mihirsavadi/fancyGradHat/pcb_resources/fancyGradCap_rev2/fancyGradCap_rev2_ControlsPower.kicad_sch

## KiCad design pcb_resources/fancyGradCap_rev2/fancyGradCap_rev2_ControlsPower.kicad_sch (2022-02-05)

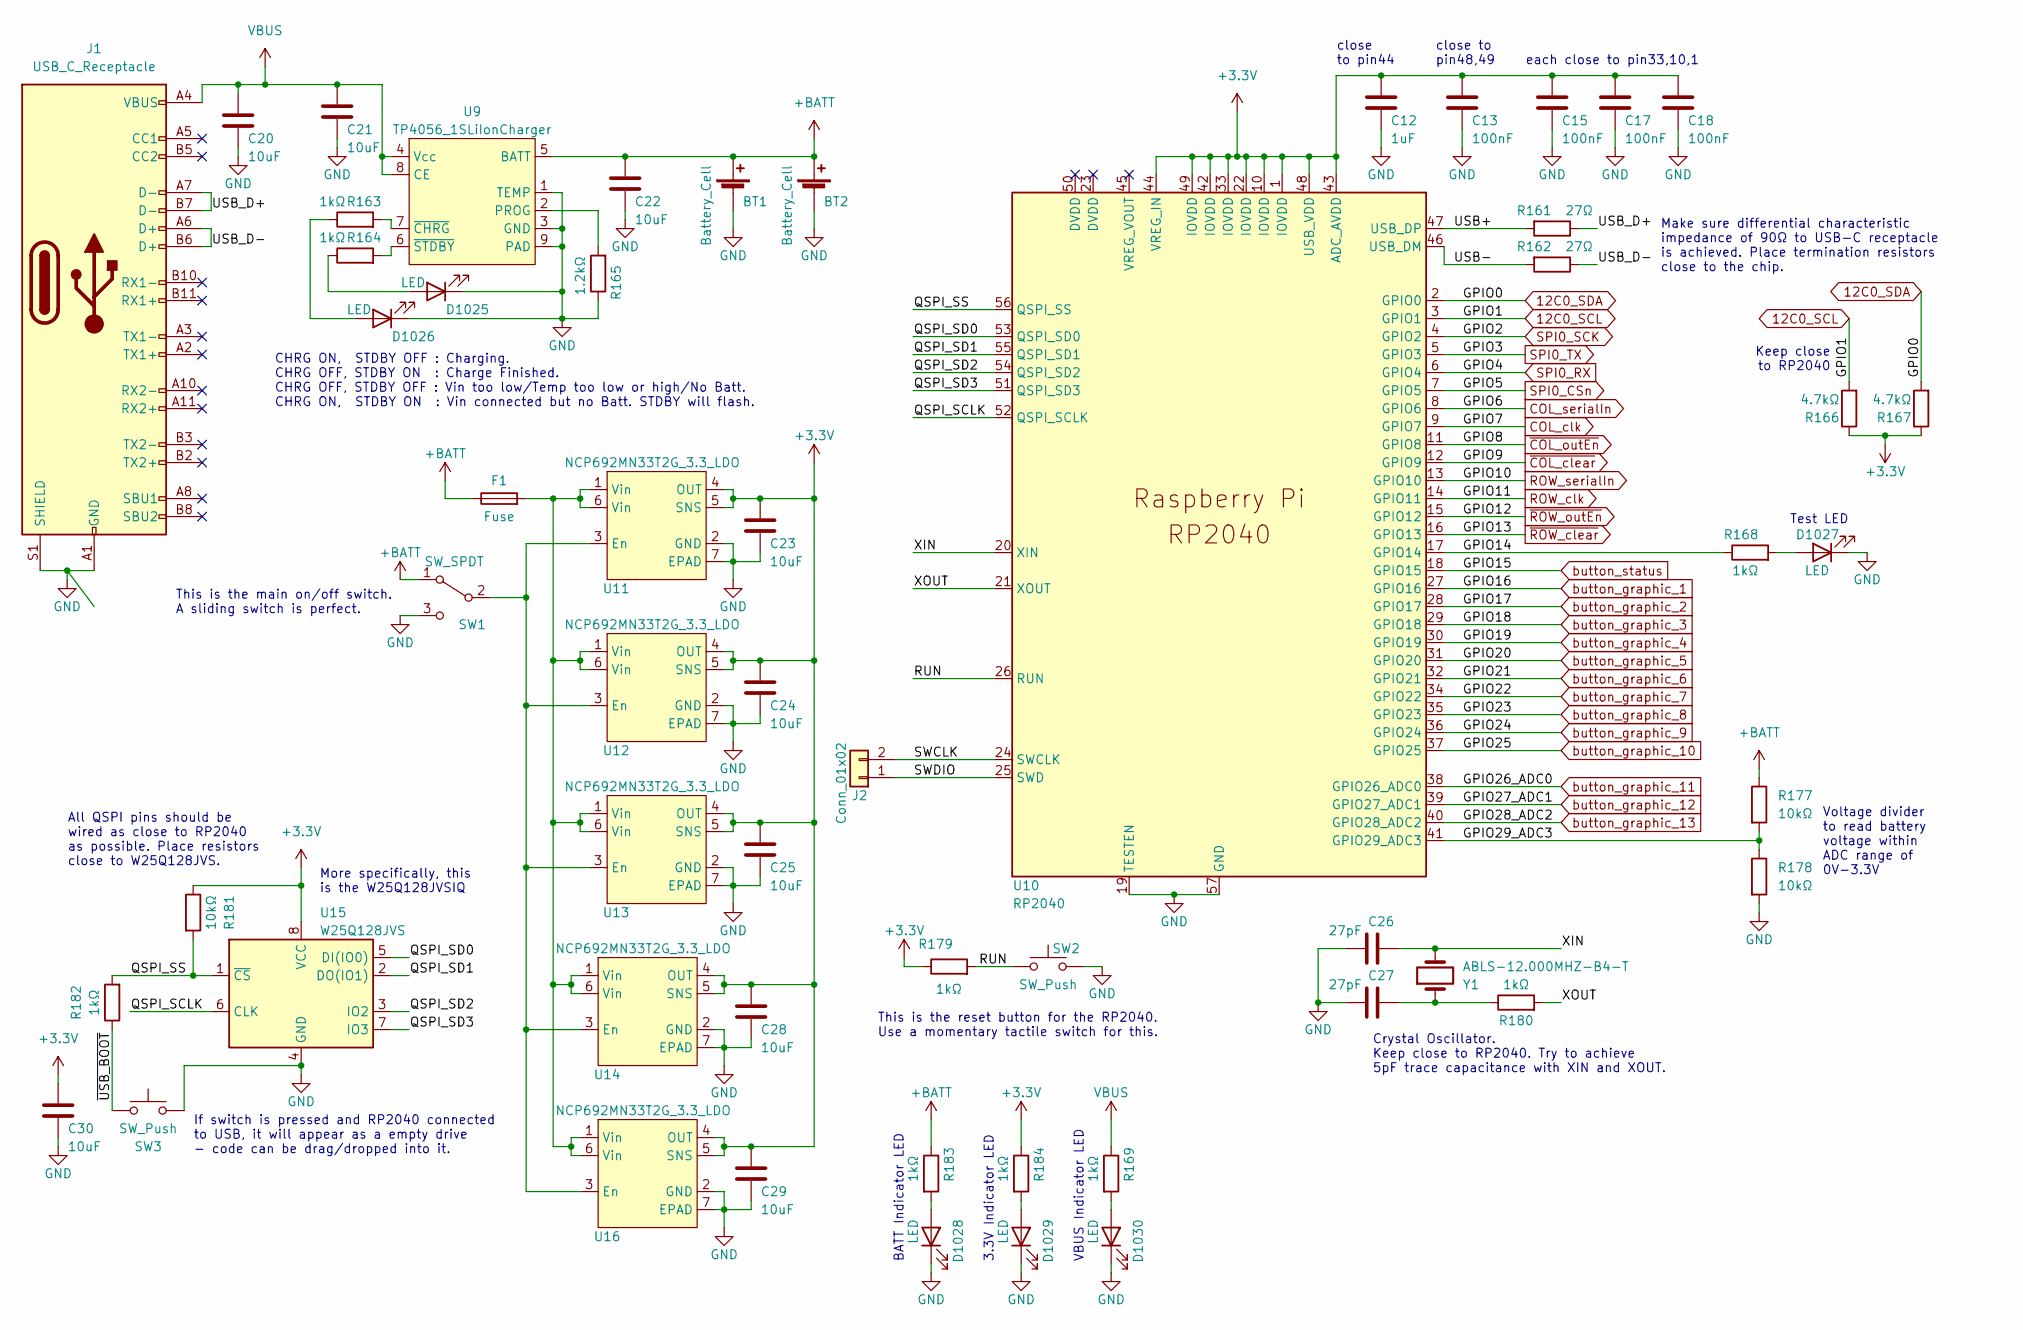
[picture p14: schematic fancyGradCap_rev2_ControlsPower.kicad_sch]

Parts:
BT1, BT2: Battery_Cell; BatteryHolder_Keystone_1042_1x18650
C12: 1uF; C_0603_1608Metric_Pad1.08x0.95mm_HandSolder
C13, C15, C17, C18: 100nF; C_0603_1608Metric_Pad1.08x0.95mm_HandSolder
C20, C21, C22, C23, C24, C25, C28, C29, C30: 10uF; C_0603_1608Metric_Pad1.08x0.95mm_HandSolder
C26, C27: 27pF; C_0603_1608Metric_Pad1.08x0.95mm_HandSolder
D1025, D1026, D1027, D1028, D1029, D1030: LED; LED_0603_1608Metric_Pad1.05x0.95mm_HandSolder
F1: Fuse; FuseHolder_Keystone_3550-2
J1: USB_C_Receptacle; USB_C_3.1_10137062-00021LF
J2: Conn_01x02; PinHeader_1x02_P2.54mm_Vertical
R161, R162: 27Ω; R_0603_1608Metric_Pad0.98x0.95mm_HandSolder
R163, R164, R168, R169, R179, R180, R182, R183, R184: 1kΩ; R_0603_1608Metric_Pad0.98x0.95mm_HandSolder
R165: 1.2kΩ; R_0603_1608Metric_Pad0.98x0.95mm_HandSolder
R166, R167: 4.7kΩ; R_0603_1608Metric_Pad0.98x0.95mm_HandSolder
R177, R178, R181: 10kΩ; R_0603_1608Metric_Pad0.98x0.95mm_HandSolder
SW1: SW_SPDT; SW_SPDT_CK-JS102011SAQN
SW2, SW3: SW_Push; SW_PUSH_1P1T_NO_6x6mm_H5mm
U9: TP4056_1SLiIonCharger
U10: RP2040; MCU_RP2040_QFN40P700X700X90-57N
U11, U12, U13, U14, U16: NCP692MN33T2G_3.3_LDO; DFN-6-1EP_3x3mm_P0.95mm_EP1.7x2.6mm
U15: W25Q128JVS; SOIC-8_5.23x5.23mm_P1.27mm
Y1: ABLS-12.000MHZ-B4-T; Crystal_ABLS-12.000MHZ-B4-T

Connections:
12C0_SCL: R166.2, U10.3 (GPIO1)
12C0_SDA: R167.2, U10.2 (GPIO0)
+3.3V: C12.1, C13.1, C15.1, C17.1, C18.1, C23.1, C24.1, C25.1, C28.1, C29.1, C30.1, R166.1, R167.1, R179.1, R181.1, R184.1, U10.1 (IOVDD), U10.10 (IOVDD), U10.22 (IOVDD), U10.33 (IOVDD), U10.42 (IOVDD), U10.43 (ADC_AVDD), U10.44 (VREG_IN), U10.48 (USB_VDD), U10.49 (IOVDD), U11.4 (OUT), U11.5 (SNS), U12.4 (OUT), U12.5 (SNS), U13.4 (OUT), U13.5 (SNS), U14.4 (OUT), U14.5 (SNS), U15.8 (VCC), U16.4 (OUT), U16.5 (SNS)
+BATT: BT1.1 (+), BT2.1 (+), C22.1, F1.1, R177.1, R183.1, SW1.1 (A), U9.5 (BATT)
COL_clk: U10.9 (GPIO7)
COL_serialIn: U10.8 (GPIO6)
GND: BT1.2 (-), BT2.2 (-), C12.2, C13.2, C15.2, C17.2, C18.2, C20.2, C21.2, C22.2, C23.2, C24.2, C25.2, C26.1, C27.1, C28.2, C29.2, C30.2, D1025.1 (K), D1026.1 (K), D1027.1 (K), D1028.1 (K), D1029.1 (K), D1030.1 (K), J1.A1 (GND), J1.A12 (GND), J1.B1 (GND), J1.B12 (GND), J1.S1 (SHIELD), R165.1, R178.2, SW1.3 (C), SW2.2, SW3.2, U9.1 (TEMP), U9.3 (GND), U9.9 (PAD), U10.19 (TESTEN), U10.57 (GND), U11.2 (GND), U11.7 (EPAD), U12.2 (GND), U12.7 (EPAD), U13.2 (GND), U13.7 (EPAD), U14.2 (GND), U14.7 (EPAD), U15.4 (GND), U16.2 (GND), U16.7 (EPAD)
GPIO14: R168.1, U10.17 (GPIO14)
GPIO29_ADC3: R177.2, R178.1, U10.41 (GPIO29_ADC3)
unnamed: C27.2, R180.1, Y1.1
unnamed: D1025.2 (A), R164.1
unnamed: D1026.2 (A), R163.1
unnamed: D1027.2 (A), R168.2
unnamed: D1028.2 (A), R183.2
unnamed: D1029.2 (A), R184.2
unnamed: D1030.2 (A), R169.2
unnamed: F1.2, U11.1 (Vin), U11.6 (Vin), U12.1 (Vin), U12.6 (Vin), U13.1 (Vin), U13.6 (Vin), U14.1 (Vin), U14.6 (Vin), U16.1 (Vin), U16.6 (Vin)
unnamed: R163.2, U9.7 (~CHRG)
unnamed: R164.2, U9.6 (~STDBY)
unnamed: R165.2, U9.2 (PROG)
unnamed: SW1.2 (B), U11.3 (En), U12.3 (En), U13.3 (En), U14.3 (En), U16.3 (En)
QSPI_SCLK: U10.52 (QSPI_SCLK), U15.6 (CLK)
QSPI_SD0: U10.53 (QSPI_SD0), U15.5 (DI(IO0))
QSPI_SD1: U10.55 (QSPI_SD1), U15.2 (DO(IO1))
QSPI_SD2: U10.54 (QSPI_SD2), U15.3 (IO2)
QSPI_SD3: U10.51 (QSPI_SD3), U15.7 (IO3)
QSPI_SS: R181.2, R182.2, U10.56 (QSPI_SS), U15.1 (~CS)
ROW_clk: U10.14 (GPIO11)
ROW_serialIn: U10.13 (GPIO10)
RUN: R179.2, SW2.1, U10.26 (RUN)
SPI0_CSn: U10.7 (GPIO5)
SPI0_RX: U10.6 (GPIO4)
SPI0_SCK: U10.4 (GPIO2)
SPI0_TX: U10.5 (GPIO3)
SWCLK: J2.2, U10.24 (SWCLK)
SWDIO: J2.1, U10.25 (SWD)
USB+: R161.2, U10.47 (USB_DP)
USB-: R162.2, U10.46 (USB_DM)
USB_D+: J1.A7 (D-), J1.B7 (D-), R161.1
USB_D-: J1.A6 (D+), J1.B6 (D+), R162.1
VBUS: C20.1, C21.1, J1.A4 (VBUS), J1.A9 (VBUS), J1.B4 (VBUS), J1.B9 (VBUS), R169.1, U9.4 (Vcc), U9.8 (CE)
XIN: C26.2, U10.20 (XIN), Y1.2
XOUT: R180.2, U10.21 (XOUT)
button_graphic_1: U10.27 (GPIO16)
button_graphic_2: U10.28 (GPIO17)
button_graphic_3: U10.29 (GPIO18)
button_graphic_4: U10.30 (GPIO19)
button_graphic_5: U10.31 (GPIO20)
button_graphic_6: U10.32 (GPIO21)
button_graphic_7: U10.34 (GPIO22)
button_graphic_8: U10.35 (GPIO23)
button_graphic_9: U10.36 (GPIO24)
button_graphic_10: U10.37 (GPIO25)
button_graphic_11: U10.38 (GPIO26_ADC0)
button_graphic_12: U10.39 (GPIO27_ADC1)
button_graphic_13: U10.40 (GPIO28_ADC2)
button_status: U10.18 (GPIO15)
~COL_clear: U10.12 (GPIO9)
~COL_outEn: U10.11 (GPIO8)
~ROW_clear: U10.16 (GPIO13)
~ROW_outEn: U10.15 (GPIO12)
~USB_BOOT: R182.1, SW3.1

Notes on the sheet:
Voltage divider to read battery voltage within ADC range of 0V-3.3V
Test LED
BATT Indicator LED
Crystal Oscillator. Keep close to RP2040. Try to achieve 5pF trace capacitance with XIN and XOUT.
Keep close to RP2040
close to pin44
Make sure differential characteristic impedance of 90Ω to USB-C receptacle is achieved. Place termination resistors close to the chip.
All QSPI pins should be wired as close to RP2040 as possible. Place resistors close to W25Q128JVS.
This is the reset button for the RP2040. Use a momentary tactile switch for this.
More specifically, this is the W25Q128JVSIQ
If switch is pressed and RP2040 connected to USB, it will appear as a empty drive - code can be drag/dropped into it.
CHRG ON, STDBY OFF : Charging. CHRG OFF, STDBY ON : Charge Finished. CHRG OFF, STDBY OFF : Vin too low/Temp too low or high/No Batt. CHRG ON, STDBY ON : Vin connected but no Batt. STDBY will flash.
3.3V Indicator LED
each close to pin33,10,1
This is the main on/off switch. A sliding switch is perfect.
close to pin48,49
VBUS Indicator LED
