mihirsavadi/fancyGradHat/pcb_resources/fancyGradCap_rev2/fancyGradCap_rev2_LEDDriverCircuitry.kicad_sch

## KiCad design pcb_resources/fancyGradCap_rev2/fancyGradCap_rev2_LEDDriverCircuitry.kicad_sch (2022-02-05)

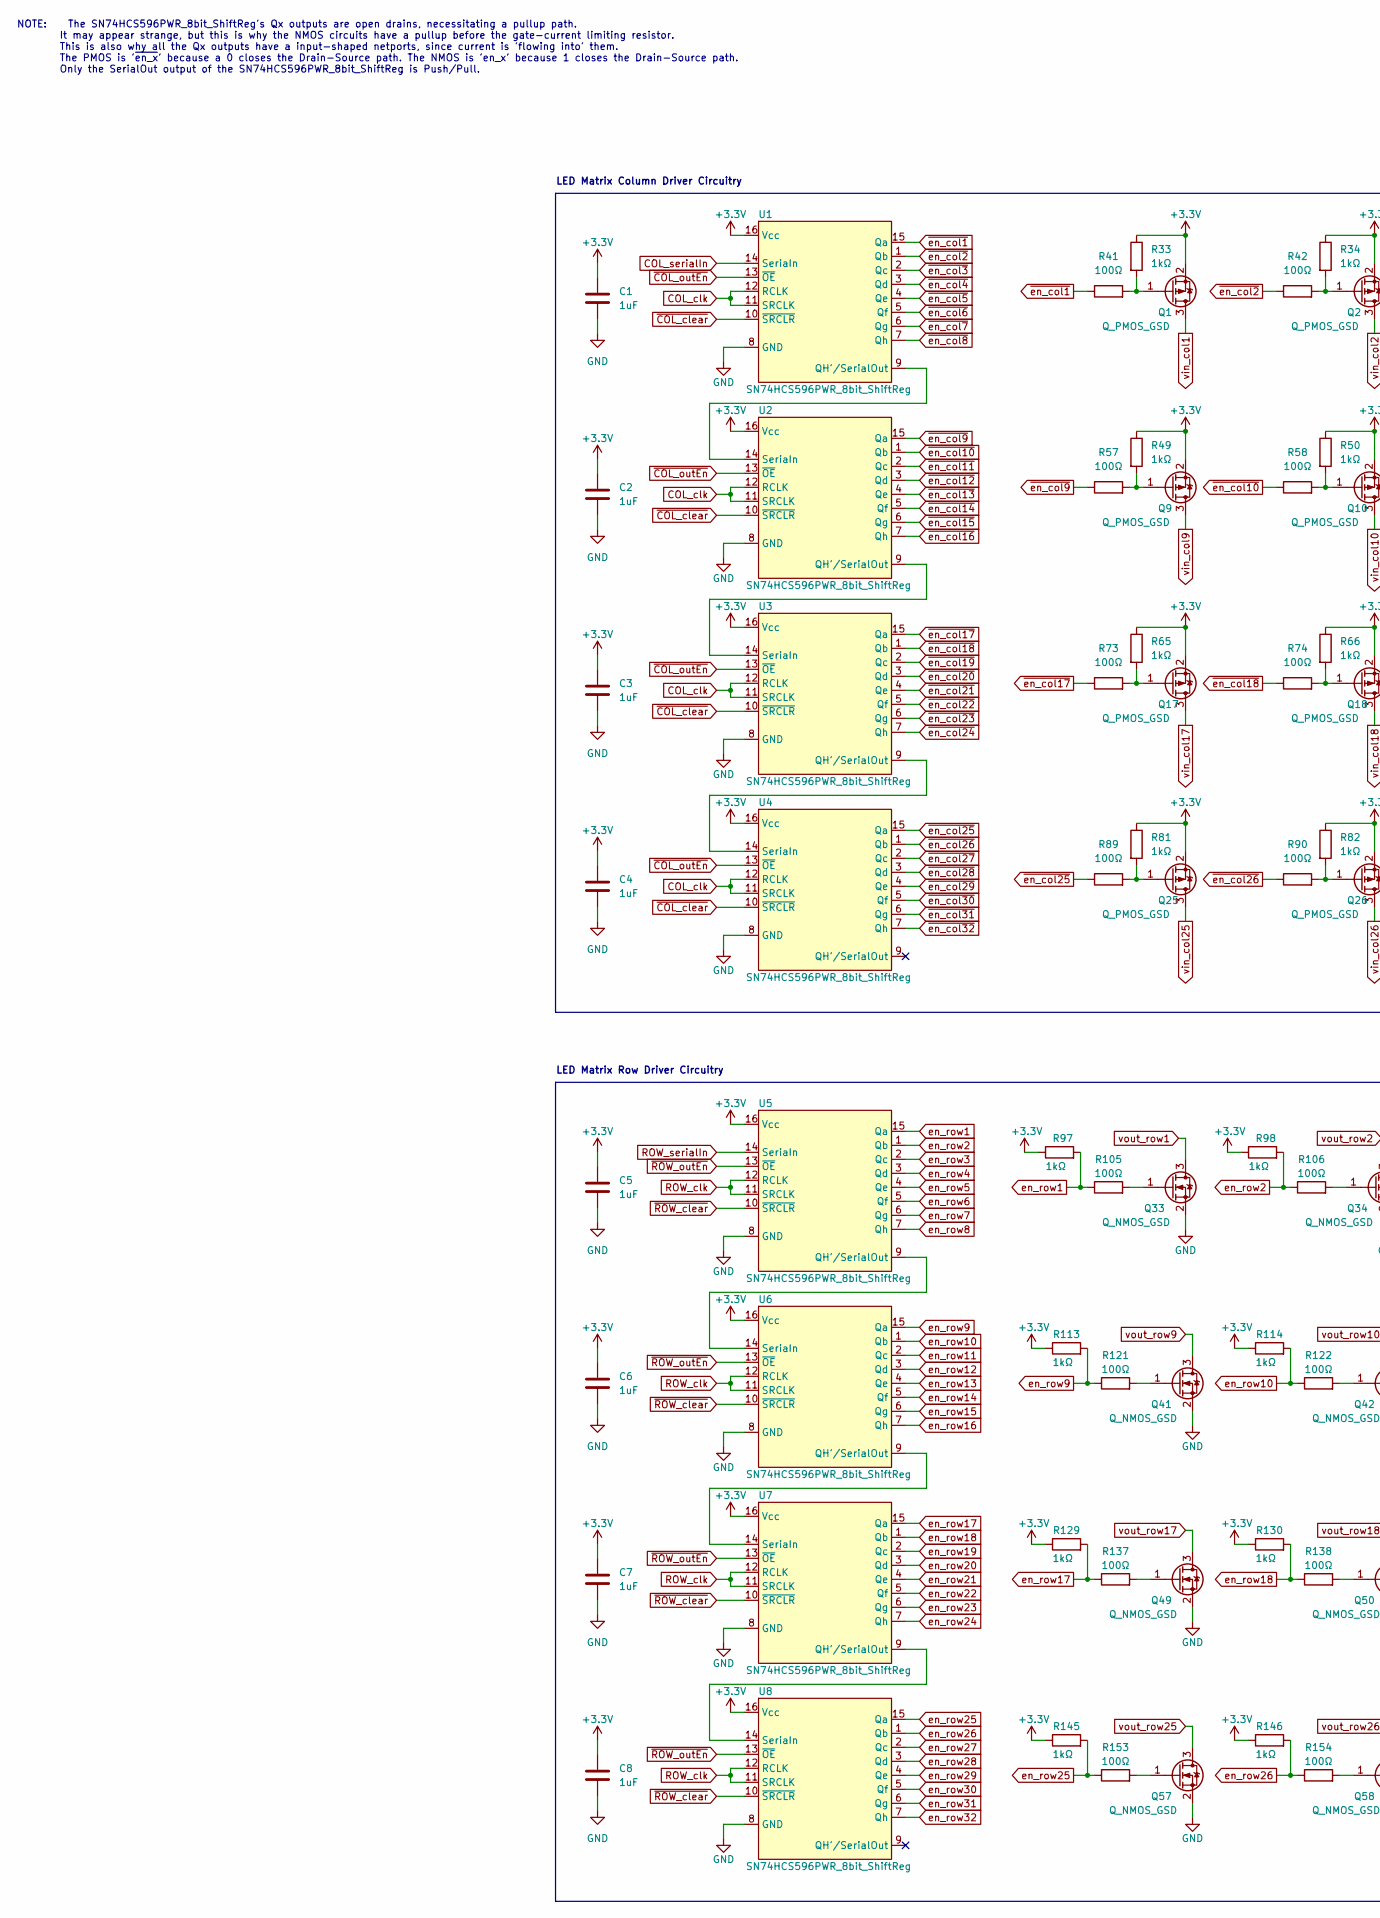
[picture p15: schematic fancyGradCap_rev2_LEDDriverCircuitry.kicad_sch, part in row 1, column 1]

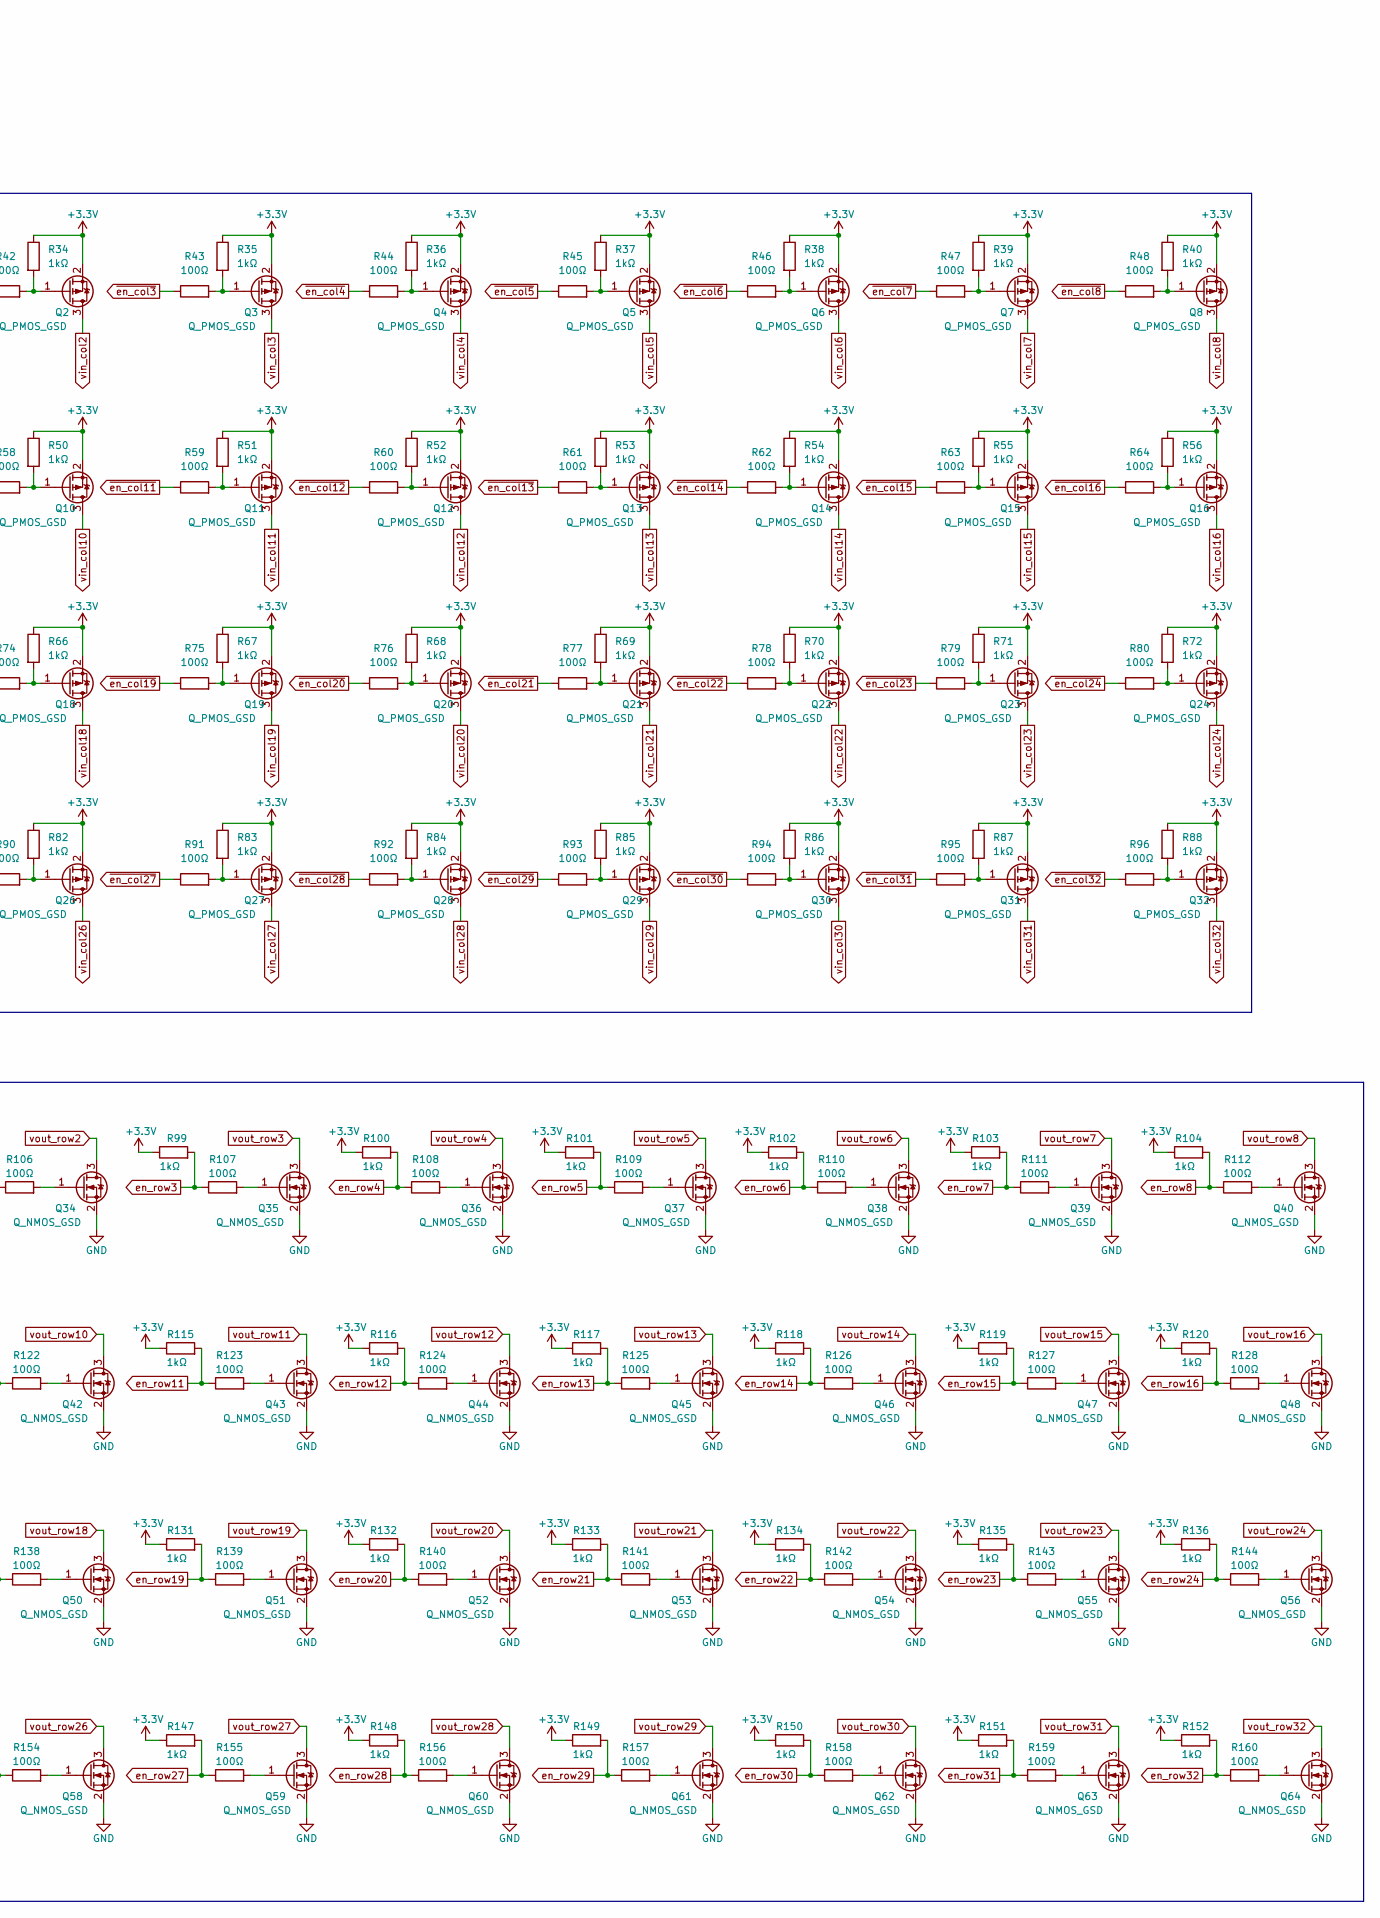
[picture p16: schematic fancyGradCap_rev2_LEDDriverCircuitry.kicad_sch, part in row 1, column 2]

Parts:
C1, C2, C3, C4, C5, C6, C7, C8: 1uF; C_0603_1608Metric_Pad1.08x0.95mm_HandSolder
Q1, Q2, Q3, Q4, Q5, Q6, Q7, Q8, Q9, Q10, Q11, Q12, Q13, Q14, Q15, Q16, Q17, Q18, Q19, Q20, Q21, Q22, Q23, Q24, Q25, Q26, Q27, Q28, Q29, Q30, Q31, Q32: Q_PMOS_GSD; SOT-23
Q33, Q34, Q35, Q36, Q37, Q38, Q39, Q40, Q41, Q42, Q43, Q44, Q45, Q46, Q47, Q48, Q49, Q50, Q51, Q52, Q53, Q54, Q55, Q56, Q57, Q58, Q59, Q60, Q61, Q62, Q63, Q64: Q_NMOS_GSD; SOT-23
R33, R34, R35, R36, R37, R38, R39, R40, R49, R50, R51, R52, R53, R54, R55, R56, R65, R66, R67, R68, R69, R70, R71, R72, R81, R82, R83, R84, R85, R86, R87, R88, R97, R98, R99, R100, R101, R102, R103, R104, R113, R114, R115, R116, R117, R118, R119, R120, R129, R130, R131, R132, R133, R134, R135, R136, R145, R146, R147, R148, R149, R150, R151, R152: 1kΩ; R_0603_1608Metric_Pad0.98x0.95mm_HandSolder
R41, R42, R43, R44, R45, R46, R47, R48, R57, R58, R59, R60, R61, R62, R63, R64, R73, R74, R75, R76, R77, R78, R79, R80, R89, R90, R91, R92, R93, R94, R95, R96, R105, R106, R107, R108, R109, R110, R111, R112, R121, R122, R123, R124, R125, R126, R127, R128, R137, R138, R139, R140, R141, R142, R143, R144, R153, R154, R155, R156, R157, R158, R159, R160: 100Ω; R_0603_1608Metric_Pad0.98x0.95mm_HandSolder
U1, U2, U3, U4, U5, U6, U7, U8: SN74HCS596PWR_8bit_ShiftReg; TSSOP-16_4.4x5mm_P0.65mm

Connections:
+3.3V: C1.1, C2.1, C3.1, C4.1, C5.1, C6.1, C7.1, C8.1, Q1.2 (S), Q2.2 (S), Q3.2 (S), Q4.2 (S), Q5.2 (S), Q6.2 (S), Q7.2 (S), Q8.2 (S), Q9.2 (S), Q10.2 (S), Q11.2 (S), Q12.2 (S), Q13.2 (S), Q14.2 (S), Q15.2 (S), Q16.2 (S), Q17.2 (S), Q18.2 (S), Q19.2 (S), Q20.2 (S), Q21.2 (S), Q22.2 (S), Q23.2 (S), Q24.2 (S), Q25.2 (S), Q26.2 (S), Q27.2 (S), Q28.2 (S), Q29.2 (S), Q30.2 (S), Q31.2 (S), Q32.2 (S), R33.1, R34.1, R35.1, R36.1, R37.1, R38.1, R39.1, R40.1, R49.1, R50.1, R51.1, R52.1, R53.1, R54.1, R55.1, R56.1, R65.1, R66.1, R67.1, R68.1, R69.1, R70.1, R71.1, R72.1, R81.1, R82.1, R83.1, R84.1, R85.1, R86.1, R87.1, R88.1, R97.1, R98.1, R99.1, R100.1, R101.1, R102.1, R103.1, R104.1, R113.1, R114.1, R115.1, R116.1, R117.1, R118.1, R119.1, R120.1, R129.1, R130.1, R131.1, R132.1, R133.1, R134.1, R135.1, R136.1, R145.1, R146.1, R147.1, R148.1, R149.1, R150.1, R151.1, R152.1, U1.16 (Vcc), U2.16 (Vcc), U3.16 (Vcc), U4.16 (Vcc), U5.16 (Vcc), U6.16 (Vcc), U7.16 (Vcc), U8.16 (Vcc)
COL_clk: U1.11 (SRCLK), U1.12 (RCLK), U2.11 (SRCLK), U2.12 (RCLK), U3.11 (SRCLK), U3.12 (RCLK), U4.11 (SRCLK), U4.12 (RCLK)
COL_serialIn: U1.14 (SeriaIn)
GND: C1.2, C2.2, C3.2, C4.2, C5.2, C6.2, C7.2, C8.2, Q33.2 (S), Q34.2 (S), Q35.2 (S), Q36.2 (S), Q37.2 (S), Q38.2 (S), Q39.2 (S), Q40.2 (S), Q41.2 (S), Q42.2 (S), Q43.2 (S), Q44.2 (S), Q45.2 (S), Q46.2 (S), Q47.2 (S), Q48.2 (S), Q49.2 (S), Q50.2 (S), Q51.2 (S), Q52.2 (S), Q53.2 (S), Q54.2 (S), Q55.2 (S), Q56.2 (S), Q57.2 (S), Q58.2 (S), Q59.2 (S), Q60.2 (S), Q61.2 (S), Q62.2 (S), Q63.2 (S), Q64.2 (S), U1.8 (GND), U2.8 (GND), U3.8 (GND), U4.8 (GND), U5.8 (GND), U6.8 (GND), U7.8 (GND), U8.8 (GND)
unnamed: Q1.1 (G), R33.2, R41.2
unnamed: Q2.1 (G), R34.2, R42.2
unnamed: Q3.1 (G), R35.2, R43.2
unnamed: Q4.1 (G), R36.2, R44.2
unnamed: Q5.1 (G), R37.2, R45.2
unnamed: Q6.1 (G), R38.2, R46.2
unnamed: Q7.1 (G), R39.2, R47.2
unnamed: Q8.1 (G), R40.2, R48.2
unnamed: Q9.1 (G), R49.2, R57.2
unnamed: Q10.1 (G), R50.2, R58.2
unnamed: Q11.1 (G), R51.2, R59.2
unnamed: Q12.1 (G), R52.2, R60.2
unnamed: Q13.1 (G), R53.2, R61.2
unnamed: Q14.1 (G), R54.2, R62.2
unnamed: Q15.1 (G), R55.2, R63.2
unnamed: Q16.1 (G), R56.2, R64.2
unnamed: Q17.1 (G), R65.2, R73.2
unnamed: Q18.1 (G), R66.2, R74.2
unnamed: Q19.1 (G), R67.2, R75.2
unnamed: Q20.1 (G), R68.2, R76.2
unnamed: Q21.1 (G), R69.2, R77.2
unnamed: Q22.1 (G), R70.2, R78.2
unnamed: Q23.1 (G), R71.2, R79.2
unnamed: Q24.1 (G), R72.2, R80.2
unnamed: Q25.1 (G), R81.2, R89.2
unnamed: Q26.1 (G), R82.2, R90.2
unnamed: Q27.1 (G), R83.2, R91.2
unnamed: Q28.1 (G), R84.2, R92.2
unnamed: Q29.1 (G), R85.2, R93.2
unnamed: Q30.1 (G), R86.2, R94.2
unnamed: Q31.1 (G), R87.2, R95.2
unnamed: Q32.1 (G), R88.2, R96.2
unnamed: Q33.1 (G), R105.2
unnamed: Q34.1 (G), R106.2
unnamed: Q35.1 (G), R107.2
unnamed: Q36.1 (G), R108.2
unnamed: Q37.1 (G), R109.2
unnamed: Q38.1 (G), R110.2
unnamed: Q39.1 (G), R111.2
unnamed: Q40.1 (G), R112.2
unnamed: Q41.1 (G), R121.2
unnamed: Q42.1 (G), R122.2
unnamed: Q43.1 (G), R123.2
unnamed: Q44.1 (G), R124.2
unnamed: Q45.1 (G), R125.2
unnamed: Q46.1 (G), R126.2
unnamed: Q47.1 (G), R127.2
unnamed: Q48.1 (G), R128.2
unnamed: Q49.1 (G), R137.2
unnamed: Q50.1 (G), R138.2
unnamed: Q51.1 (G), R139.2
unnamed: Q52.1 (G), R140.2
unnamed: Q53.1 (G), R141.2
unnamed: Q54.1 (G), R142.2
unnamed: Q55.1 (G), R143.2
unnamed: Q56.1 (G), R144.2
unnamed: Q57.1 (G), R153.2
unnamed: Q58.1 (G), R154.2
unnamed: Q59.1 (G), R155.2
unnamed: Q60.1 (G), R156.2
unnamed: Q61.1 (G), R157.2
unnamed: Q62.1 (G), R158.2
unnamed: Q63.1 (G), R159.2
unnamed: Q64.1 (G), R160.2
unnamed: U1.9 (QH'/SerialOut), U2.14 (SeriaIn)
unnamed: U2.9 (QH'/SerialOut), U3.14 (SeriaIn)
unnamed: U3.9 (QH'/SerialOut), U4.14 (SeriaIn)
unnamed: U5.9 (QH'/SerialOut), U6.14 (SeriaIn)
unnamed: U6.9 (QH'/SerialOut), U7.14 (SeriaIn)
unnamed: U7.9 (QH'/SerialOut), U8.14 (SeriaIn)
ROW_clk: U5.11 (SRCLK), U5.12 (RCLK), U6.11 (SRCLK), U6.12 (RCLK), U7.11 (SRCLK), U7.12 (RCLK), U8.11 (SRCLK), U8.12 (RCLK)
ROW_serialIn: U5.14 (SeriaIn)
en_row1: R97.2, R105.1, U5.15 (Qa)
en_row2: R98.2, R106.1, U5.1 (Qb)
en_row3: R99.2, R107.1, U5.2 (Qc)
en_row4: R100.2, R108.1, U5.3 (Qd)
en_row5: R101.2, R109.1, U5.4 (Qe)
en_row6: R102.2, R110.1, U5.5 (Qf)
en_row7: R103.2, R111.1, U5.6 (Qg)
en_row8: R104.2, R112.1, U5.7 (Qh)
en_row9: R113.2, R121.1, U6.15 (Qa)
en_row10: R114.2, R122.1, U6.1 (Qb)
en_row11: R115.2, R123.1, U6.2 (Qc)
en_row12: R116.2, R124.1, U6.3 (Qd)
en_row13: R117.2, R125.1, U6.4 (Qe)
en_row14: R118.2, R126.1, U6.5 (Qf)
en_row15: R119.2, R127.1, U6.6 (Qg)
en_row16: R120.2, R128.1, U6.7 (Qh)
en_row17: R129.2, R137.1, U7.15 (Qa)
en_row18: R130.2, R138.1, U7.1 (Qb)
en_row19: R131.2, R139.1, U7.2 (Qc)
en_row20: R132.2, R140.1, U7.3 (Qd)
en_row21: R133.2, R141.1, U7.4 (Qe)
en_row22: R134.2, R142.1, U7.5 (Qf)
en_row23: R135.2, R143.1, U7.6 (Qg)
en_row24: R136.2, R144.1, U7.7 (Qh)
en_row25: R145.2, R153.1, U8.15 (Qa)
en_row26: R146.2, R154.1, U8.1 (Qb)
en_row27: R147.2, R155.1, U8.2 (Qc)
en_row28: R148.2, R156.1, U8.3 (Qd)
en_row29: R149.2, R157.1, U8.4 (Qe)
en_row30: R150.2, R158.1, U8.5 (Qf)
en_row31: R151.2, R159.1, U8.6 (Qg)
en_row32: R152.2, R160.1, U8.7 (Qh)
vin_col1: Q1.3 (D)
vin_col2: Q2.3 (D)
vin_col3: Q3.3 (D)
vin_col4: Q4.3 (D)
vin_col5: Q5.3 (D)
vin_col6: Q6.3 (D)
vin_col7: Q7.3 (D)
vin_col8: Q8.3 (D)
vin_col9: Q9.3 (D)
vin_col10: Q10.3 (D)
vin_col11: Q11.3 (D)
vin_col12: Q12.3 (D)
vin_col13: Q13.3 (D)
vin_col14: Q14.3 (D)
vin_col15: Q15.3 (D)
vin_col16: Q16.3 (D)
vin_col17: Q17.3 (D)
vin_col18: Q18.3 (D)
vin_col19: Q19.3 (D)
vin_col20: Q20.3 (D)
vin_col21: Q21.3 (D)
vin_col22: Q22.3 (D)
vin_col23: Q23.3 (D)
vin_col24: Q24.3 (D)
vin_col25: Q25.3 (D)
vin_col26: Q26.3 (D)
vin_col27: Q27.3 (D)
vin_col28: Q28.3 (D)
vin_col29: Q29.3 (D)
vin_col30: Q30.3 (D)
vin_col31: Q31.3 (D)
vin_col32: Q32.3 (D)
vout_row1: Q33.3 (D)
vout_row2: Q34.3 (D)
vout_row3: Q35.3 (D)
vout_row4: Q36.3 (D)
vout_row5: Q37.3 (D)
vout_row6: Q38.3 (D)
vout_row7: Q39.3 (D)
vout_row8: Q40.3 (D)
vout_row9: Q41.3 (D)
vout_row10: Q42.3 (D)
vout_row11: Q43.3 (D)
vout_row12: Q44.3 (D)
vout_row13: Q45.3 (D)
vout_row14: Q46.3 (D)
vout_row15: Q47.3 (D)
vout_row16: Q48.3 (D)
vout_row17: Q49.3 (D)
vout_row18: Q50.3 (D)
vout_row19: Q51.3 (D)
vout_row20: Q52.3 (D)
vout_row21: Q53.3 (D)
vout_row22: Q54.3 (D)
vout_row23: Q55.3 (D)
vout_row24: Q56.3 (D)
vout_row25: Q57.3 (D)
vout_row26: Q58.3 (D)
vout_row27: Q59.3 (D)
vout_row28: Q60.3 (D)
vout_row29: Q61.3 (D)
vout_row30: Q62.3 (D)
vout_row31: Q63.3 (D)
vout_row32: Q64.3 (D)
~COL_clear: U1.10 (~SRCLR), U2.10 (~SRCLR), U3.10 (~SRCLR), U4.10 (~SRCLR)
~COL_outEn: U1.13 (~OE), U2.13 (~OE), U3.13 (~OE), U4.13 (~OE)
~ROW_clear: U5.10 (~SRCLR), U6.10 (~SRCLR), U7.10 (~SRCLR), U8.10 (~SRCLR)
~ROW_outEn: U5.13 (~OE), U6.13 (~OE), U7.13 (~OE), U8.13 (~OE)
~en_col1: R41.1, U1.15 (Qa)
~en_col2: R42.1, U1.1 (Qb)
~en_col3: R43.1, U1.2 (Qc)
~en_col4: R44.1, U1.3 (Qd)
~en_col5: R45.1, U1.4 (Qe)
~en_col6: R46.1, U1.5 (Qf)
~en_col7: R47.1, U1.6 (Qg)
~en_col8: R48.1, U1.7 (Qh)
~en_col9: R57.1, U2.15 (Qa)
~en_col10: R58.1, U2.1 (Qb)
~en_col11: R59.1, U2.2 (Qc)
~en_col12: R60.1, U2.3 (Qd)
~en_col13: R61.1, U2.4 (Qe)
~en_col14: R62.1, U2.5 (Qf)
~en_col15: R63.1, U2.6 (Qg)
~en_col16: R64.1, U2.7 (Qh)
~en_col17: R73.1, U3.15 (Qa)
~en_col18: R74.1, U3.1 (Qb)
~en_col19: R75.1, U3.2 (Qc)
~en_col20: R76.1, U3.3 (Qd)
~en_col21: R77.1, U3.4 (Qe)
~en_col22: R78.1, U3.5 (Qf)
~en_col23: R79.1, U3.6 (Qg)
~en_col24: R80.1, U3.7 (Qh)
~en_col25: R89.1, U4.15 (Qa)
~en_col26: R90.1, U4.1 (Qb)
~en_col27: R91.1, U4.2 (Qc)
~en_col28: R92.1, U4.3 (Qd)
~en_col29: R93.1, U4.4 (Qe)
~en_col30: R94.1, U4.5 (Qf)
~en_col31: R95.1, U4.6 (Qg)
~en_col32: R96.1, U4.7 (Qh)

Notes on the sheet:
LED Matrix Column Driver Circuitry
LED Matrix Row Driver Circuitry
NOTE: The SN74HCS596PWR_8bit_ShiftReg's Qx outputs are open drains, necessitating a pullup path. It may appear strange, but this is why the NMOS circuits have a pullup before the gate-current limiting resistor. This is also why all the Qx outputs have a input-shaped netports, since current is 'flow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
