mihirsavadi/fancyGradHat/pcb_resources/fancyGradCap_rev2/fancyGradCap_rev2_LEDMATRIX.kicad_sch

## KiCad design pcb_resources/fancyGradCap_rev2/fancyGradCap_rev2_LEDMATRIX.kicad_sch (2022-02-05)

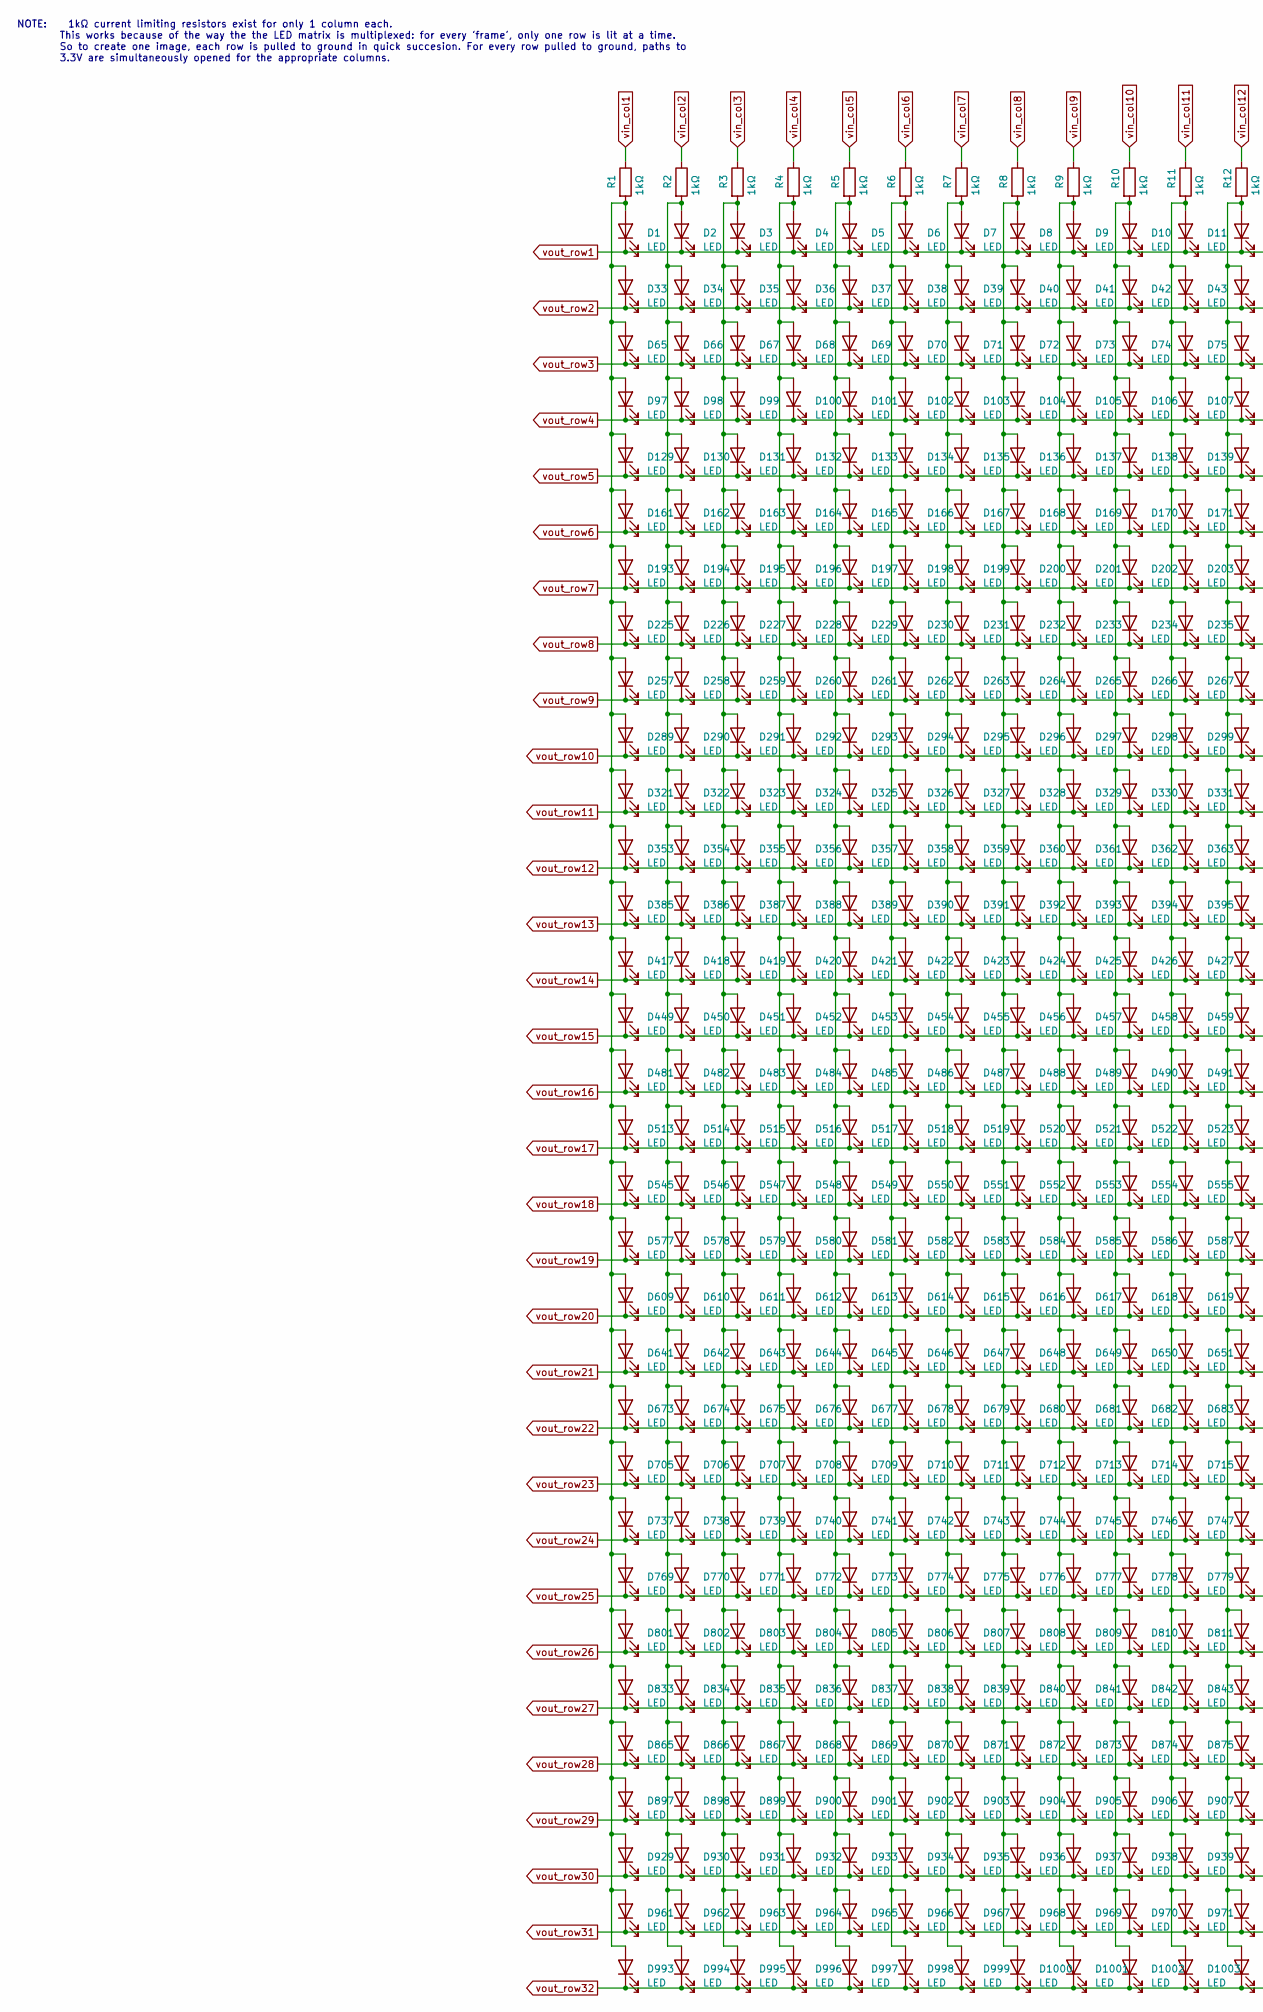
[picture p17: schematic fancyGradCap_rev2_LEDMATRIX.kicad_sch, part in row 1, column 1]

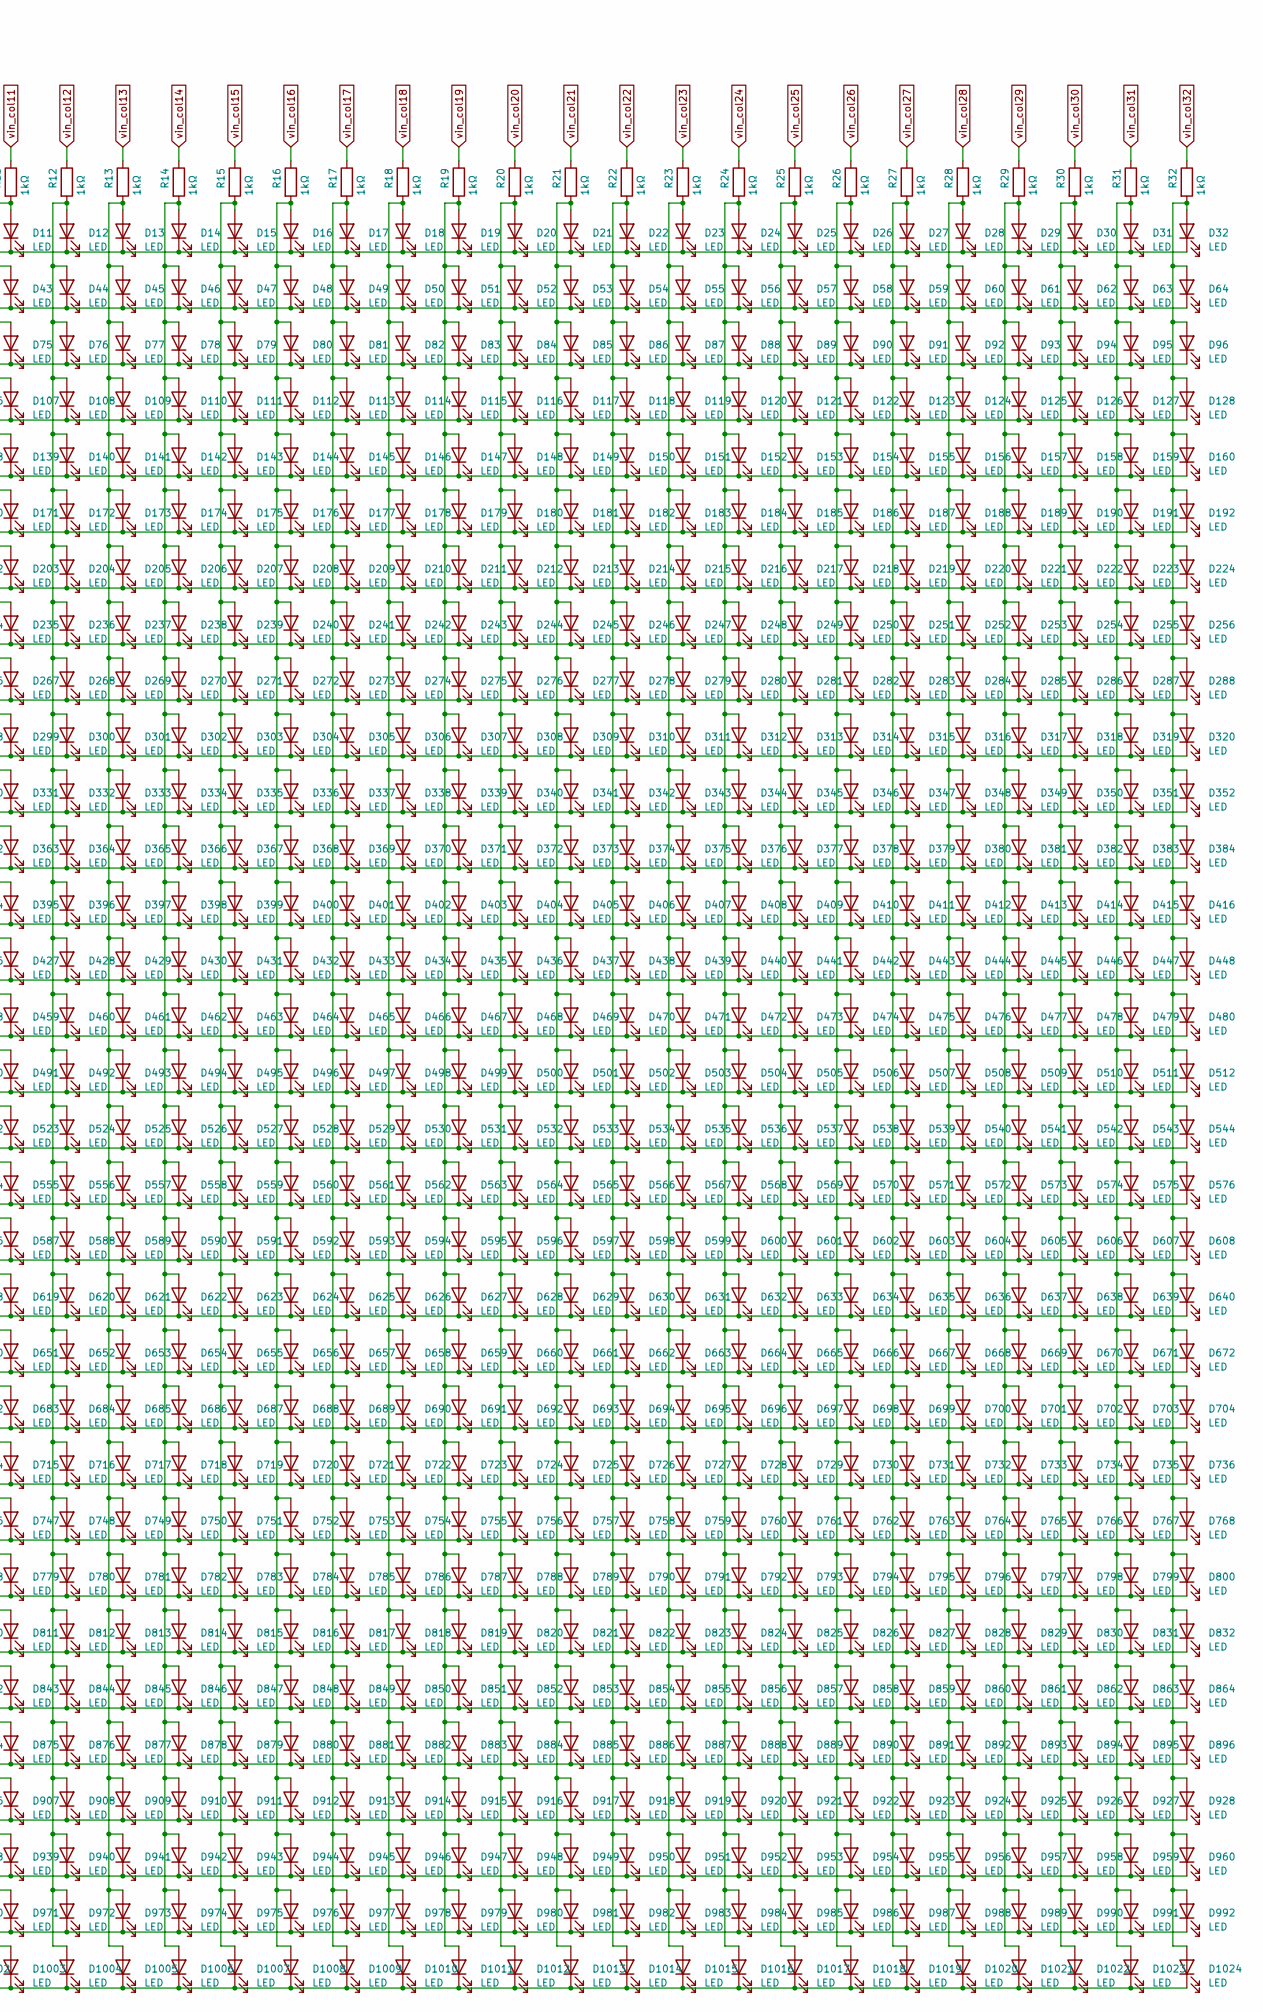
[picture p18: schematic fancyGradCap_rev2_LEDMATRIX.kicad_sch, part in row 1, column 2]

Parts:
D1, D2, D3, D4, D5, D6, D7, D8, D9, D10, D11, D12, D13, D14, D15, D16, D17, D18, D19, D20, D21, D22, D23, D24, D25, D26, D27, D28, D29, D30, D31, D32, D33, D34, D35, D36, D37, D38, D39, D40, D41, D42, D43, D44, D45, D46, D47, D48, D49, D50, D51, D52, D53, D54, D55, D56, D57, D58, D59, D60, D61, D62, D63, D64, D65, D66, D67, D68, D69, D70, D71, D72, D73, D74, D75, D76, D77, D78, D79, D80, D81, D82, D83, D84, D85, D86, D87, D88, D89, D90, D91, D92, D93, D94, D95, D96, D97, D98, D99, D100, D101, D102, D103, D104, D105, D106, D107, D108, D109, D110, D111, D112, D113, D114, D115, D116, D117, D118, D119, D120, D121, D122, D123, D124, D125, D126, D127, D128, D129, D130, D131, D132, D133, D134, D135, D136, D137, D138, D139, D140, D141, D142, D143, D144, D145, D146, D147, D148, D149, D150, D151, D152, D153, D154, D155, D156, D157, D158, D159, D160, D161, D162, D163, D164, D165, D166, D167, D168, D169, D170, D171, D172, D173, D174, D175, D176, D177, D178, D179, D180, D181, D182, D183, D184, D185, D186, D187, D188, D189, D190, D191, D192, D193, D194, D195, D196, D197, D198, D199, D200, D201, D202, D203, D204, D205, D206, D207, D208, D209, D210, D211, D212, D213, D214, D215, D216, D217, D218, D219, D220, D221, D222, D223, D224, D225, D226, D227, D228, D229, D230, D231, D232, D233, D234, D235, D236, D237, D238, D239, D240, D241, D242, D243, D244, D245, D246, D247, D248, D249, D250, D251, D252, D253, D254, D255, D256, D257, D258, D259, D260, D261, D262, D263, D264, D265, D266, D267, D268, D269, D270, D271, D272, D273, D274, D275, D276, D277, D278, D279, D280, D281, D282, D283, D284, D285, D286, D287, D288, D289, D290, D291, D292, D293, D294, D295, D296, D297, D298, D299, D300, D301, D302, D303, D304, D305, D306, D307, D308, D309, D310, D311, D312, D313, D314, D315, D316, D317, D318, D319, D320, D321, D322, D323, D324, D325, D326, D327, D328, D329, D330, D331, D332, D333, D334, D335, D336, D337, D338, D339, D340, D341, D342, D343, D344, D345, D346, D347, D348, D349, D350, D351, D352, D353, D354, D355, D356, D357, D358, D359, D360, D361, D362, D363, D364, D365, D366, D367, D368, D369, D370, D371, D372, D373, D374, D375, D376, D377, D378, D379, D380, D381, D382, D383, D384, D385, D386, D387, D388, D389, D390, D391, D392, D393, D394, D395, D396, D397, D398, D399, D400, D401, D402, D403, D404, D405, D406, D407, D408, D409, D410, D411, D412, D413, D414, D415, D416, D417, D418, D419, D420, D421, D422, D423, D424, D425, D426, D427, D428, D429, D430, D431, D432, D433, D434, D435, D436, D437, D438, D439, D440, D441, D442, D443, D444, D445, D446, D447, D448, D449, D450, D451, D452, D453, D454, D455, D456, D457, D458, D459, D460, D461, D462, D463, D464, D465, D466, D467, D468, D469, D470, D471, D472, D473, D474, D475, D476, D477, D478, D479, D480, D481, D482, D483, D484, D485, D486, D487, D488, D489, D490, D491, D492, D493, D494, D495, D496, D497, D498, D499, D500, D501, D502, D503, D504, D505, D506, D507, D508, D509, D510, D511, D512, D513, D514, D515, D516, D517, D518, D519, D520, D521, D522, D523, D524, D525, D526, D527, D528, D529, D530, D531, D532, D533, D534, D535, D536, D537, D538, D539, D540, D541, D542, D543, D544, D545, D546, D547, D548, D549, D550, D551, D552, D553, D554, D555, D556, D557, D558, D559, D560, D561, D562, D563, D564, D565, D566, D567, D568, D569, D570, D571, D572, D573, D574, D575, D576, D577, D578, D579, D580, D581, D582, D583, D584, D585, D586, D587, D588, D589, D590, D591, D592, D593, D594, D595, D596, D597, D598, D599, D600, D601, D602, D603, D604, D605, D606, D607, D608, D609, D610, D611, D612, D613, D614, D615, D616, D617, D618, D619, D620, D621, D622, D623, D624, D625, D626, D627, D628, D629, D630, D631, D632, D633, D634, D635, D636, D637, D638, D639, D640, D641, D642, D643, D644, D645, D646, D647, D648, D649, D650, D651, D652, D653, D654, D655, D656, D657, D658, D659, D660, D661, D662, D663, D664, D665, D666, D667, D668, D669, D670, D671, D672, D673, D674, D675, D676, D677, D678, D679, D680, D681, D682, D683, D684, D685, D686, D687, D688, D689, D690, D691, D692, D693, D694, D695, D696, D697, D698, D699, D700, D701, D702, D703, D704, D705, D706, D707, D708, D709, D710, D711, D712, D713, D714, D715, D716, D717, D718, D719, D720, D721, D722, D723, D724, D725, D726, D727, D728, D729, D730, D731, D732, D733, D734, D735, D736, D737, D738, D739, D740, D741, D742, D743, D744, D745, D746, D747, D748, D749, D750, D751, D752, D753, D754, D755, D756, D757, D758, D759, D760, D761, D762, D763, D764, D765, D766, D767, D768, D769, D770, D771, D772, D773, D774, D775, D776, D777, D778, D779, D780, D781, D782, D783, D784, D785, D786, D787, D788, D789, D790, D791, D792, D793, D794, D795, D796, D797, D798, D799, D800, D801, D802, D803, D804, D805, D806, D807, D808, D809, D810, D811, D812, D813, D814, D815, D816, D817, D818, D819, D820, D821, D822, D823, D824, D825, D826, D827, D828, D829, D830, D831, D832, D833, D834, D835, D836, D837, D838, D839, D840, D841, D842, D843, D844, D845, D846, D847, D848, D849, D850, D851, D852, D853, D854, D855, D856, D857, D858, D859, D860, D861, D862, D863, D864, D865, D866, D867, D868, D869, D870, D871, D872, D873, D874, D875, D876, D877, D878, D879, D880, D881, D882, D883, D884, D885, D886, D887, D888, D889, D890, D891, D892, D893, D894, D895, D896, D897, D898, D899, D900, D901, D902, D903, D904, D905, D906, D907, D908, D909, D910, D911, D912, D913, D914, D915, D916, D917, D918, D919, D920, D921, D922, D923, D924, D925, D926, D927, D928, D929, D930, D931, D932, D933, D934, D935, D936, D937, D938, D939, D940, D941, D942, D943, D944, D945, D946, D947, D948, D949, D950, D951, D952, D953, D954, D955, D956, D957, D958, D959, D960, D961, D962, D963, D964, D965, D966, D967, D968, D969, D970, D971, D972, D973, D974, D975, D976, D977, D978, D979, D980, D981, D982, D983, D984, D985, D986, D987, D988, D989, D990, D991, D992, D993, D994, D995, D996, D997, D998, D999, D1000, D1001, D1002, D1003, D1004, D1005, D1006, D1007, D1008, D1009, D1010, D1011, D1012, D1013, D1014, D1015, D1016, D1017, D1018, D1019, D1020, D1021, D1022, D1023, D1024: LED; LED_0603_1608Metric_Pad1.05x0.95mm_HandSolder
R1, R2, R3, R4, R5, R6, R7, R8, R9, R10, R11, R12, R13, R14, R15, R16, R17, R18, R19, R20, R21, R22, R23, R24, R25, R26, R27, R28, R29, R30, R31, R32: 1kΩ; R_0603_1608Metric_Pad0.98x0.95mm_HandSolder

Connections:
unnamed: D1.2 (A), D33.2 (A), D65.2 (A), D97.2 (A), D129.2 (A), D161.2 (A), D193.2 (A), D225.2 (A), D257.2 (A), D289.2 (A), D321.2 (A), D353.2 (A), D385.2 (A), D417.2 (A), D449.2 (A), D481.2 (A), D513.2 (A), D545.2 (A), D577.2 (A), D609.2 (A), D641.2 (A), D673.2 (A), D705.2 (A), D737.2 (A), D769.2 (A), D801.2 (A), D833.2 (A), D865.2 (A), D897.2 (A), D929.2 (A), D961.2 (A), D993.2 (A), R1.2
unnamed: D10.2 (A), D42.2 (A), D74.2 (A), D106.2 (A), D138.2 (A), D170.2 (A), D202.2 (A), D234.2 (A), D266.2 (A), D298.2 (A), D330.2 (A), D362.2 (A), D394.2 (A), D426.2 (A), D458.2 (A), D490.2 (A), D522.2 (A), D554.2 (A), D586.2 (A), D618.2 (A), D650.2 (A), D682.2 (A), D714.2 (A), D746.2 (A), D778.2 (A), D810.2 (A), D842.2 (A), D874.2 (A), D906.2 (A), D938.2 (A), D970.2 (A), D1002.2 (A), R10.2
unnamed: D4.2 (A), D36.2 (A), D68.2 (A), D100.2 (A), D132.2 (A), D164.2 (A), D196.2 (A), D228.2 (A), D260.2 (A), D292.2 (A), D324.2 (A), D356.2 (A), D388.2 (A), D420.2 (A), D452.2 (A), D484.2 (A), D516.2 (A), D548.2 (A), D580.2 (A), D612.2 (A), D644.2 (A), D676.2 (A), D708.2 (A), D740.2 (A), D772.2 (A), D804.2 (A), D836.2 (A), D868.2 (A), D900.2 (A), D932.2 (A), D964.2 (A), D996.2 (A), R4.2
unnamed: D5.2 (A), D37.2 (A), D69.2 (A), D101.2 (A), D133.2 (A), D165.2 (A), D197.2 (A), D229.2 (A), D261.2 (A), D293.2 (A), D325.2 (A), D357.2 (A), D389.2 (A), D421.2 (A), D453.2 (A), D485.2 (A), D517.2 (A), D549.2 (A), D581.2 (A), D613.2 (A), D645.2 (A), D677.2 (A), D709.2 (A), D741.2 (A), D773.2 (A), D805.2 (A), D837.2 (A), D869.2 (A), D901.2 (A), D933.2 (A), D965.2 (A), D997.2 (A), R5.2
unnamed: D6.2 (A), D38.2 (A), D70.2 (A), D102.2 (A), D134.2 (A), D166.2 (A), D198.2 (A), D230.2 (A), D262.2 (A), D294.2 (A), D326.2 (A), D358.2 (A), D390.2 (A), D422.2 (A), D454.2 (A), D486.2 (A), D518.2 (A), D550.2 (A), D582.2 (A), D614.2 (A), D646.2 (A), D678.2 (A), D710.2 (A), D742.2 (A), D774.2 (A), D806.2 (A), D838.2 (A), D870.2 (A), D902.2 (A), D934.2 (A), D966.2 (A), D998.2 (A), R6.2
unnamed: D7.2 (A), D39.2 (A), D71.2 (A), D103.2 (A), D135.2 (A), D167.2 (A), D199.2 (A), D231.2 (A), D263.2 (A), D295.2 (A), D327.2 (A), D359.2 (A), D391.2 (A), D423.2 (A), D455.2 (A), D487.2 (A), D519.2 (A), D551.2 (A), D583.2 (A), D615.2 (A), D647.2 (A), D679.2 (A), D711.2 (A), D743.2 (A), D775.2 (A), D807.2 (A), D839.2 (A), D871.2 (A), D903.2 (A), D935.2 (A), D967.2 (A), D999.2 (A), R7.2
unnamed: D2.2 (A), D34.2 (A), D66.2 (A), D98.2 (A), D130.2 (A), D162.2 (A), D194.2 (A), D226.2 (A), D258.2 (A), D290.2 (A), D322.2 (A), D354.2 (A), D386.2 (A), D418.2 (A), D450.2 (A), D482.2 (A), D514.2 (A), D546.2 (A), D578.2 (A), D610.2 (A), D642.2 (A), D674.2 (A), D706.2 (A), D738.2 (A), D770.2 (A), D802.2 (A), D834.2 (A), D866.2 (A), D898.2 (A), D930.2 (A), D962.2 (A), D994.2 (A), R2.2
unnamed: D3.2 (A), D35.2 (A), D67.2 (A), D99.2 (A), D131.2 (A), D163.2 (A), D195.2 (A), D227.2 (A), D259.2 (A), D291.2 (A), D323.2 (A), D355.2 (A), D387.2 (A), D419.2 (A), D451.2 (A), D483.2 (A), D515.2 (A), D547.2 (A), D579.2 (A), D611.2 (A), D643.2 (A), D675.2 (A), D707.2 (A), D739.2 (A), D771.2 (A), D803.2 (A), D835.2 (A), D867.2 (A), D899.2 (A), D931.2 (A), D963.2 (A), D995.2 (A), R3.2
unnamed: D8.2 (A), D40.2 (A), D72.2 (A), D104.2 (A), D136.2 (A), D168.2 (A), D200.2 (A), D232.2 (A), D264.2 (A), D296.2 (A), D328.2 (A), D360.2 (A), D392.2 (A), D424.2 (A), D456.2 (A), D488.2 (A), D520.2 (A), D552.2 (A), D584.2 (A), D616.2 (A), D648.2 (A), D680.2 (A), D712.2 (A), D744.2 (A), D776.2 (A), D808.2 (A), D840.2 (A), D872.2 (A), D904.2 (A), D936.2 (A), D968.2 (A), D1000.2 (A), R8.2
unnamed: D9.2 (A), D41.2 (A), D73.2 (A), D105.2 (A), D137.2 (A), D169.2 (A), D201.2 (A), D233.2 (A), D265.2 (A), D297.2 (A), D329.2 (A), D361.2 (A), D393.2 (A), D425.2 (A), D457.2 (A), D489.2 (A), D521.2 (A), D553.2 (A), D585.2 (A), D617.2 (A), D649.2 (A), D681.2 (A), D713.2 (A), D745.2 (A), D777.2 (A), D809.2 (A), D841.2 (A), D873.2 (A), D905.2 (A), D937.2 (A), D969.2 (A), D1001.2 (A), R9.2
unnamed: D11.2 (A), D43.2 (A), D75.2 (A), D107.2 (A), D139.2 (A), D171.2 (A), D203.2 (A), D235.2 (A), D267.2 (A), D299.2 (A), D331.2 (A), D363.2 (A), D395.2 (A), D427.2 (A), D459.2 (A), D491.2 (A), D523.2 (A), D555.2 (A), D587.2 (A), D619.2 (A), D651.2 (A), D683.2 (A), D715.2 (A), D747.2 (A), D779.2 (A), D811.2 (A), D843.2 (A), D875.2 (A), D907.2 (A), D939.2 (A), D971.2 (A), D1003.2 (A), R11.2
unnamed: D12.2 (A), D44.2 (A), D76.2 (A), D108.2 (A), D140.2 (A), D172.2 (A), D204.2 (A), D236.2 (A), D268.2 (A), D300.2 (A), D332.2 (A), D364.2 (A), D396.2 (A), D428.2 (A), D460.2 (A), D492.2 (A), D524.2 (A), D556.2 (A), D588.2 (A), D620.2 (A), D652.2 (A), D684.2 (A), D716.2 (A), D748.2 (A), D780.2 (A), D812.2 (A), D844.2 (A), D876.2 (A), D908.2 (A), D940.2 (A), D972.2 (A), D1004.2 (A), R12.2
unnamed: D13.2 (A), D45.2 (A), D77.2 (A), D109.2 (A), D141.2 (A), D173.2 (A), D205.2 (A), D237.2 (A), D269.2 (A), D301.2 (A), D333.2 (A), D365.2 (A), D397.2 (A), D429.2 (A), D461.2 (A), D493.2 (A), D525.2 (A), D557.2 (A), D589.2 (A), D621.2 (A), D653.2 (A), D685.2 (A), D717.2 (A), D749.2 (A), D781.2 (A), D813.2 (A), D845.2 (A), D877.2 (A), D909.2 (A), D941.2 (A), D973.2 (A), D1005.2 (A), R13.2
unnamed: D14.2 (A), D46.2 (A), D78.2 (A), D110.2 (A), D142.2 (A), D174.2 (A), D206.2 (A), D238.2 (A), D270.2 (A), D302.2 (A), D334.2 (A), D366.2 (A), D398.2 (A), D430.2 (A), D462.2 (A), D494.2 (A), D526.2 (A), D558.2 (A), D590.2 (A), D622.2 (A), D654.2 (A), D686.2 (A), D718.2 (A), D750.2 (A), D782.2 (A), D814.2 (A), D846.2 (A), D878.2 (A), D910.2 (A), D942.2 (A), D974.2 (A), D1006.2 (A), R14.2
unnamed: D15.2 (A), D47.2 (A), D79.2 (A), D111.2 (A), D143.2 (A), D175.2 (A), D207.2 (A), D239.2 (A), D271.2 (A), D303.2 (A), D335.2 (A), D367.2 (A), D399.2 (A), D431.2 (A), D463.2 (A), D495.2 (A), D527.2 (A), D559.2 (A), D591.2 (A), D623.2 (A), D655.2 (A), D687.2 (A), D719.2 (A), D751.2 (A), D783.2 (A), D815.2 (A), D847.2 (A), D879.2 (A), D911.2 (A), D943.2 (A), D975.2 (A), D1007.2 (A), R15.2
unnamed: D16.2 (A), D48.2 (A), D80.2 (A), D112.2 (A), D144.2 (A), D176.2 (A), D208.2 (A), D240.2 (A), D272.2 (A), D304.2 (A), D336.2 (A), D368.2 (A), D400.2 (A), D432.2 (A), D464.2 (A), D496.2 (A), D528.2 (A), D560.2 (A), D592.2 (A), D624.2 (A), D656.2 (A), D688.2 (A), D720.2 (A), D752.2 (A), D784.2 (A), D816.2 (A), D848.2 (A), D880.2 (A), D912.2 (A), D944.2 (A), D976.2 (A), D1008.2 (A), R16.2
unnamed: D17.2 (A), D49.2 (A), D81.2 (A), D113.2 (A), D145.2 (A), D177.2 (A), D209.2 (A), D241.2 (A), D273.2 (A), D305.2 (A), D337.2 (A), D369.2 (A), D401.2 (A), D433.2 (A), D465.2 (A), D497.2 (A), D529.2 (A), D561.2 (A), D593.2 (A), D625.2 (A), D657.2 (A), D689.2 (A), D721.2 (A), D753.2 (A), D785.2 (A), D817.2 (A), D849.2 (A), D881.2 (A), D913.2 (A), D945.2 (A), D977.2 (A), D1009.2 (A), R17.2
unnamed: D18.2 (A), D50.2 (A), D82.2 (A), D114.2 (A), D146.2 (A), D178.2 (A), D210.2 (A), D242.2 (A), D274.2 (A), D306.2 (A), D338.2 (A), D370.2 (A), D402.2 (A), D434.2 (A), D466.2 (A), D498.2 (A), D530.2 (A), D562.2 (A), D594.2 (A), D626.2 (A), D658.2 (A), D690.2 (A), D722.2 (A), D754.2 (A), D786.2 (A), D818.2 (A), D850.2 (A), D882.2 (A), D914.2 (A), D946.2 (A), D978.2 (A), D1010.2 (A), R18.2
unnamed: D19.2 (A), D51.2 (A), D83.2 (A), D115.2 (A), D147.2 (A), D179.2 (A), D211.2 (A), D243.2 (A), D275.2 (A), D307.2 (A), D339.2 (A), D371.2 (A), D403.2 (A), D435.2 (A), D467.2 (A), D499.2 (A), D531.2 (A), D563.2 (A), D595.2 (A), D627.2 (A), D659.2 (A), D691.2 (A), D723.2 (A), D755.2 (A), D787.2 (A), D819.2 (A), D851.2 (A), D883.2 (A), D915.2 (A), D947.2 (A), D979.2 (A), D1011.2 (A), R19.2
unnamed: D20.2 (A), D52.2 (A), D84.2 (A), D116.2 (A), D148.2 (A), D180.2 (A), D212.2 (A), D244.2 (A), D276.2 (A), D308.2 (A), D340.2 (A), D372.2 (A), D404.2 (A), D436.2 (A), D468.2 (A), D500.2 (A), D532.2 (A), D564.2 (A), D596.2 (A), D628.2 (A), D660.2 (A), D692.2 (A), D724.2 (A), D756.2 (A), D788.2 (A), D820.2 (A), D852.2 (A), D884.2 (A), D916.2 (A), D948.2 (A), D980.2 (A), D1012.2 (A), R20.2
unnamed: D21.2 (A), D53.2 (A), D85.2 (A), D117.2 (A), D149.2 (A), D181.2 (A), D213.2 (A), D245.2 (A), D277.2 (A), D309.2 (A), D341.2 (A), D373.2 (A), D405.2 (A), D437.2 (A), D469.2 (A), D501.2 (A), D533.2 (A), D565.2 (A), D597.2 (A), D629.2 (A), D661.2 (A), D693.2 (A), D725.2 (A), D757.2 (A), D789.2 (A), D821.2 (A), D853.2 (A), D885.2 (A), D917.2 (A), D949.2 (A), D981.2 (A), D1013.2 (A), R21.2
unnamed: D22.2 (A), D54.2 (A), D86.2 (A), D118.2 (A), D150.2 (A), D182.2 (A), D214.2 (A), D246.2 (A), D278.2 (A), D310.2 (A), D342.2 (A), D374.2 (A), D406.2 (A), D438.2 (A), D470.2 (A), D502.2 (A), D534.2 (A), D566.2 (A), D598.2 (A), D630.2 (A), D662.2 (A), D694.2 (A), D726.2 (A), D758.2 (A), D790.2 (A), D822.2 (A), D854.2 (A), D886.2 (A), D918.2 (A), D950.2 (A), D982.2 (A), D1014.2 (A), R22.2
unnamed: D23.2 (A), D55.2 (A), D87.2 (A), D119.2 (A), D151.2 (A), D183.2 (A), D215.2 (A), D247.2 (A), D279.2 (A), D311.2 (A), D343.2 (A), D375.2 (A), D407.2 (A), D439.2 (A), D471.2 (A), D503.2 (A), D535.2 (A), D567.2 (A), D599.2 (A), D631.2 (A), D663.2 (A), D695.2 (A), D727.2 (A), D759.2 (A), D791.2 (A), D823.2 (A), D855.2 (A), D887.2 (A), D919.2 (A), D951.2 (A), D983.2 (A), D1015.2 (A), R23.2
unnamed: D24.2 (A), D56.2 (A), D88.2 (A), D120.2 (A), D152.2 (A), D184.2 (A), D216.2 (A), D248.2 (A), D280.2 (A), D312.2 (A), D344.2 (A), D376.2 (A), D408.2 (A), D440.2 (A), D472.2 (A), D504.2 (A), D536.2 (A), D568.2 (A), D600.2 (A), D632.2 (A), D664.2 (A), D696.2 (A), D728.2 (A), D760.2 (A), D792.2 (A), D824.2 (A), D856.2 (A), D888.2 (A), D920.2 (A), D952.2 (A), D984.2 (A), D1016.2 (A), R24.2
unnamed: D25.2 (A), D57.2 (A), D89.2 (A), D121.2 (A), D153.2 (A), D185.2 (A), D217.2 (A), D249.2 (A), D281.2 (A), D313.2 (A), D345.2 (A), D377.2 (A), D409.2 (A), D441.2 (A), D473.2 (A), D505.2 (A), D537.2 (A), D569.2 (A), D601.2 (A), D633.2 (A), D665.2 (A), D697.2 (A), D729.2 (A), D761.2 (A), D793.2 (A), D825.2 (A), D857.2 (A), D889.2 (A), D921.2 (A), D953.2 (A), D985.2 (A), D1017.2 (A), R25.2
unnamed: D26.2 (A), D58.2 (A), D90.2 (A), D122.2 (A), D154.2 (A), D186.2 (A), D218.2 (A), D250.2 (A), D282.2 (A), D314.2 (A), D346.2 (A), D378.2 (A), D410.2 (A), D442.2 (A), D474.2 (A), D506.2 (A), D538.2 (A), D570.2 (A), D602.2 (A), D634.2 (A), D666.2 (A), D698.2 (A), D730.2 (A), D762.2 (A), D794.2 (A), D826.2 (A), D858.2 (A), D890.2 (A), D922.2 (A), D954.2 (A), D986.2 (A), D1018.2 (A), R26.2
unnamed: D27.2 (A), D59.2 (A), D91.2 (A), D123.2 (A), D155.2 (A), D187.2 (A), D219.2 (A), D251.2 (A), D283.2 (A), D315.2 (A), D347.2 (A), D379.2 (A), D411.2 (A), D443.2 (A), D475.2 (A), D507.2 (A), D539.2 (A), D571.2 (A), D603.2 (A), D635.2 (A), D667.2 (A), D699.2 (A), D731.2 (A), D763.2 (A), D795.2 (A), D827.2 (A), D859.2 (A), D891.2 (A), D923.2 (A), D955.2 (A), D987.2 (A), D1019.2 (A), R27.2
unnamed: D28.2 (A), D60.2 (A), D92.2 (A), D124.2 (A), D156.2 (A), D188.2 (A), D220.2 (A), D252.2 (A), D284.2 (A), D316.2 (A), D348.2 (A), D380.2 (A), D412.2 (A), D444.2 (A), D476.2 (A), D508.2 (A), D540.2 (A), D572.2 (A), D604.2 (A), D636.2 (A), D668.2 (A), D700.2 (A), D732.2 (A), D764.2 (A), D796.2 (A), D828.2 (A), D860.2 (A), D892.2 (A), D924.2 (A), D956.2 (A), D988.2 (A), D1020.2 (A), R28.2
unnamed: D29.2 (A), D61.2 (A), D93.2 (A), D125.2 (A), D157.2 (A), D189.2 (A), D221.2 (A), D253.2 (A), D285.2 (A), D317.2 (A), D349.2 (A), D381.2 (A), D413.2 (A), D445.2 (A), D477.2 (A), D509.2 (A), D541.2 (A), D573.2 (A), D605.2 (A), D637.2 (A), D669.2 (A), D701.2 (A), D733.2 (A), D765.2 (A), D797.2 (A), D829.2 (A), D861.2 (A), D893.2 (A), D925.2 (A), D957.2 (A), D989.2 (A), D1021.2 (A), R29.2
unnamed: D30.2 (A), D62.2 (A), D94.2 (A), D126.2 (A), D158.2 (A), D190.2 (A), D222.2 (A), D254.2 (A), D286.2 (A), D318.2 (A), D350.2 (A), D382.2 (A), D414.2 (A), D446.2 (A), D478.2 (A), D510.2 (A), D542.2 (A), D574.2 (A), D606.2 (A), D638.2 (A), D670.2 (A), D702.2 (A), D734.2 (A), D766.2 (A), D798.2 (A), D830.2 (A), D862.2 (A), D894.2 (A), D926.2 (A), D958.2 (A), D990.2 (A), D1022.2 (A), R30.2
unnamed: D31.2 (A), D63.2 (A), D95.2 (A), D127.2 (A), D159.2 (A), D191.2 (A), D223.2 (A), D255.2 (A), D287.2 (A), D319.2 (A), D351.2 (A), D383.2 (A), D415.2 (A), D447.2 (A), D479.2 (A), D511.2 (A), D543.2 (A), D575.2 (A), D607.2 (A), D639.2 (A), D671.2 (A), D703.2 (A), D735.2 (A), D767.2 (A), D799.2 (A), D831.2 (A), D863.2 (A), D895.2 (A), D927.2 (A), D959.2 (A), D991.2 (A), D1023.2 (A), R31.2
unnamed: D32.2 (A), D64.2 (A), D96.2 (A), D128.2 (A), D160.2 (A), D192.2 (A), D224.2 (A), D256.2 (A), D288.2 (A), D320.2 (A), D352.2 (A), D384.2 (A), D416.2 (A), D448.2 (A), D480.2 (A), D512.2 (A), D544.2 (A), D576.2 (A), D608.2 (A), D640.2 (A), D672.2 (A), D704.2 (A), D736.2 (A), D768.2 (A), D800.2 (A), D832.2 (A), D864.2 (A), D896.2 (A), D928.2 (A), D960.2 (A), D992.2 (A), D1024.2 (A), R32.2
vin_col1: R1.1
vin_col2: R2.1
vin_col3: R3.1
vin_col4: R4.1
vin_col5: R5.1
vin_col6: R6.1
vin_col7: R7.1
vin_col8: R8.1
vin_col9: R9.1
vin_col10: R10.1
vin_col11: R11.1
vin_col12: R12.1
vin_col13: R13.1
vin_col14: R14.1
vin_col15: R15.1
vin_col16: R16.1
vin_col17: R17.1
vin_col18: R18.1
vin_col19: R19.1
vin_col20: R20.1
vin_col21: R21.1
vin_col22: R22.1
vin_col23: R23.1
vin_col24: R24.1
vin_col25: R25.1
vin_col26: R26.1
vin_col27: R27.1
vin_col28: R28.1
vin_col29: R29.1
vin_col30: R30.1
vin_col31: R31.1
vin_col32: R32.1
vout_row1: D1.1 (K), D2.1 (K), D3.1 (K), D4.1 (K), D5.1 (K), D6.1 (K), D7.1 (K), D8.1 (K), D9.1 (K), D10.1 (K), D11.1 (K), D12.1 (K), D13.1 (K), D14.1 (K), D15.1 (K), D16.1 (K), D17.1 (K), D18.1 (K), D19.1 (K), D20.1 (K), D21.1 (K), D22.1 (K), D23.1 (K), D24.1 (K), D25.1 (K), D26.1 (K), D27.1 (K), D28.1 (K), D29.1 (K), D30.1 (K), D31.1 (K), D32.1 (K)
vout_row2: D33.1 (K), D34.1 (K), D35.1 (K), D36.1 (K), D37.1 (K), D38.1 (K), D39.1 (K), D40.1 (K), D41.1 (K), D42.1 (K), D43.1 (K), D44.1 (K), D45.1 (K), D46.1 (K), D47.1 (K), D48.1 (K), D49.1 (K), D50.1 (K), D51.1 (K), D52.1 (K), D53.1 (K), D54.1 (K), D55.1 (K), D56.1 (K), D57.1 (K), D58.1 (K), D59.1 (K), D60.1 (K), D61.1 (K), D62.1 (K), D63.1 (K), D64.1 (K)
vout_row3: D65.1 (K), D66.1 (K), D67.1 (K), D68.1 (K), D69.1 (K), D70.1 (K), D71.1 (K), D72.1 (K), D73.1 (K), D74.1 (K), D75.1 (K), D76.1 (K), D77.1 (K), D78.1 (K), D79.1 (K), D80.1 (K), D81.1 (K), D82.1 (K), D83.1 (K), D84.1 (K), D85.1 (K), D86.1 (K), D87.1 (K), D88.1 (K), D89.1 (K), D90.1 (K), D91.1 (K), D92.1 (K), D93.1 (K), D94.1 (K), D95.1 (K), D96.1 (K)
vout_row4: D97.1 (K), D98.1 (K), D99.1 (K), D100.1 (K), D101.1 (K), D102.1 (K), D103.1 (K), D104.1 (K), D105.1 (K), D106.1 (K), D107.1 (K), D108.1 (K), D109.1 (K), D110.1 (K), D111.1 (K), D112.1 (K), D113.1 (K), D114.1 (K), D115.1 (K), D116.1 (K), D117.1 (K), D118.1 (K), D119.1 (K), D120.1 (K), D121.1 (K), D122.1 (K), D123.1 (K), D124.1 (K), D125.1 (K), D126.1 (K), D127.1 (K), D128.1 (K)
vout_row5: D129.1 (K), D130.1 (K), D131.1 (K), D132.1 (K), D133.1 (K), D134.1 (K), D135.1 (K), D136.1 (K), D137.1 (K), D138.1 (K), D139.1 (K), D140.1 (K), D141.1 (K), D142.1 (K), D143.1 (K), D144.1 (K), D145.1 (K), D146.1 (K), D147.1 (K), D148.1 (K), D149.1 (K), D150.1 (K), D151.1 (K), D152.1 (K), D153.1 (K), D154.1 (K), D155.1 (K), D156.1 (K), D157.1 (K), D158.1 (K), D159.1 (K), D160.1 (K)
vout_row6: D161.1 (K), D162.1 (K), D163.1 (K), D164.1 (K), D165.1 (K), D166.1 (K), D167.1 (K), D168.1 (K), D169.1 (K), D170.1 (K), D171.1 (K), D172.1 (K), D173.1 (K), D174.1 (K), D175.1 (K), D176.1 (K), D177.1 (K), D178.1 (K), D179.1 (K), D180.1 (K), D181.1 (K), D182.1 (K), D183.1 (K), D184.1 (K), D185.1 (K), D186.1 (K), D187.1 (K), D188.1 (K), D189.1 (K), D190.1 (K), D191.1 (K), D192.1 (K)
vout_row7: D193.1 (K), D194.1 (K), D195.1 (K), D196.1 (K), D197.1 (K), D198.1 (K), D199.1 (K), D200.1 (K), D201.1 (K), D202.1 (K), D203.1 (K), D204.1 (K), D205.1 (K), D206.1 (K), D207.1 (K), D208.1 (K), D209.1 (K), D210.1 (K), D211.1 (K), D212.1 (K), D213.1 (K), D214.1 (K), D215.1 (K), D216.1 (K), D217.1 (K), D218.1 (K), D219.1 (K), D220.1 (K), D221.1 (K), D222.1 (K), D223.1 (K), D224.1 (K)
vout_row8: D225.1 (K), D226.1 (K), D227.1 (K), D228.1 (K), D229.1 (K), D230.1 (K), D231.1 (K), D232.1 (K), D233.1 (K), D234.1 (K), D235.1 (K), D236.1 (K), D237.1 (K), D238.1 (K), D239.1 (K), D240.1 (K), D241.1 (K), D242.1 (K), D243.1 (K), D244.1 (K), D245.1 (K), D246.1 (K), D247.1 (K), D248.1 (K), D249.1 (K), D250.1 (K), D251.1 (K), D252.1 (K), D253.1 (K), D254.1 (K), D255.1 (K), D256.1 (K)
vout_row9: D257.1 (K), D258.1 (K), D259.1 (K), D260.1 (K), D261.1 (K), D262.1 (K), D263.1 (K), D264.1 (K), D265.1 (K), D266.1 (K), D267.1 (K), D268.1 (K), D269.1 (K), D270.1 (K), D271.1 (K), D272.1 (K), D273.1 (K), D274.1 (K), D275.1 (K), D276.1 (K), D277.1 (K), D278.1 (K), D279.1 (K), D280.1 (K), D281.1 (K), D282.1 (K), D283.1 (K), D284.1 (K), D285.1 (K), D286.1 (K), D287.1 (K), D288.1 (K)
vout_row10: D289.1 (K), D290.1 (K), D291.1 (K), D292.1 (K), D293.1 (K), D294.1 (K), D295.1 (K), D296.1 (K), D297.1 (K), D298.1 (K), D299.1 (K), D300.1 (K), D301.1 (K), D302.1 (K), D303.1 (K), D304.1 (K), D305.1 (K), D306.1 (K), D307.1 (K), D308.1 (K), D309.1 (K), D310.1 (K), D311.1 (K), D312.1 (K), D313.1 (K), D314.1 (K), D315.1 (K), D316.1 (K), D317.1 (K), D318.1 (K), D319.1 (K), D320.1 (K)
vout_row11: D321.1 (K), D322.1 (K), D323.1 (K), D324.1 (K), D325.1 (K), D326.1 (K), D327.1 (K), D328.1 (K), D329.1 (K), D330.1 (K), D331.1 (K), D332.1 (K), D333.1 (K), D334.1 (K), D335.1 (K), D336.1 (K), D337.1 (K), D338.1 (K), D339.1 (K), D340.1 (K), D341.1 (K), D342.1 (K), D343.1 (K), D344.1 (K), D345.1 (K), D346.1 (K), D347.1 (K), D348.1 (K), D349.1 (K), D350.1 (K), D351.1 (K), D352.1 (K)
vout_row12: D353.1 (K), D354.1 (K), D355.1 (K), D356.1 (K), D357.1 (K), D358.1 (K), D359.1 (K), D360.1 (K), D361.1 (K), D362.1 (K), D363.1 (K), D364.1 (K), D365.1 (K), D366.1 (K), D367.1 (K), D368.1 (K), D369.1 (K), D370.1 (K), D371.1 (K), D372.1 (K), D373.1 (K), D374.1 (K), D375.1 (K), D376.1 (K), D377.1 (K), D378.1 (K), D379.1 (K), D380.1 (K), D381.1 (K), D382.1 (K), D383.1 (K), D384.1 (K)
vout_row13: D385.1 (K), D386.1 (K), D387.1 (K), D388.1 (K), D389.1 (K), D390.1 (K), D391.1 (K), D392.1 (K), D393.1 (K), D394.1 (K), D395.1 (K), D396.1 (K), D397.1 (K), D398.1 (K), D399.1 (K), D400.1 (K), D401.1 (K), D402.1 (K), D403.1 (K), D404.1 (K), D405.1 (K), D406.1 (K), D407.1 (K), D408.1 (K), D409.1 (K), D410.1 (K), D411.1 (K), D412.1 (K), D413.1 (K), D414.1 (K), D415.1 (K), D416.1 (K)
vout_row14: D417.1 (K), D418.1 (K), D419.1 (K), D420.1 (K), D421.1 (K), D422.1 (K), D423.1 (K), D424.1 (K), D425.1 (K), D426.1 (K), D427.1 (K), D428.1 (K), D429.1 (K), D430.1 (K), D431.1 (K), D432.1 (K), D433.1 (K), D434.1 (K), D435.1 (K), D436.1 (K), D437.1 (K), D438.1 (K), D439.1 (K), D440.1 (K), D441.1 (K), D442.1 (K), D443.1 (K), D444.1 (K), D445.1 (K), D446.1 (K), D447.1 (K), D448.1 (K)
vout_row15: D449.1 (K), D450.1 (K), D451.1 (K), D452.1 (K), D453.1 (K), D454.1 (K), D455.1 (K), D456.1 (K), D457.1 (K), D458.1 (K), D459.1 (K), D460.1 (K), D461.1 (K), D462.1 (K), D463.1 (K), D464.1 (K), D465.1 (K), D466.1 (K), D467.1 (K), D468.1 (K), D469.1 (K), D470.1 (K), D471.1 (K), D472.1 (K), D473.1 (K), D474.1 (K), D475.1 (K), D476.1 (K), D477.1 (K), D478.1 (K), D479.1 (K), D480.1 (K)
vout_row16: D481.1 (K), D482.1 (K), D483.1 (K), D484.1 (K), D485.1 (K), D486.1 (K), D487.1 (K), D488.1 (K), D489.1 (K), D490.1 (K), D491.1 (K), D492.1 (K), D493.1 (K), D494.1 (K), D495.1 (K), D496.1 (K), D497.1 (K), D498.1 (K), D499.1 (K), D500.1 (K), D501.1 (K), D502.1 (K), D503.1 (K), D504.1 (K), D505.1 (K), D506.1 (K), D507.1 (K), D508.1 (K), D509.1 (K), D510.1 (K), D511.1 (K), D512.1 (K)
vout_row17: D513.1 (K), D514.1 (K), D515.1 (K), D516.1 (K), D517.1 (K), D518.1 (K), D519.1 (K), D520.1 (K), D521.1 (K), D522.1 (K), D523.1 (K), D524.1 (K), D525.1 (K), D526.1 (K), D527.1 (K), D528.1 (K), D529.1 (K), D530.1 (K), D531.1 (K), D532.1 (K), D533.1 (K), D534.1 (K), D535.1 (K), D536.1 (K), D537.1 (K), D538.1 (K), D539.1 (K), D540.1 (K), D541.1 (K), D542.1 (K), D543.1 (K), D544.1 (K)
vout_row18: D545.1 (K), D546.1 (K), D547.1 (K), D548.1 (K), D549.1 (K), D550.1 (K), D551.1 (K), D552.1 (K), D553.1 (K), D554.1 (K), D555.1 (K), D556.1 (K), D557.1 (K), D558.1 (K), D559.1 (K), D560.1 (K), D561.1 (K), D562.1 (K), D563.1 (K), D564.1 (K), D565.1 (K), D566.1 (K), D567.1 (K), D568.1 (K), D569.1 (K), D570.1 (K), D571.1 (K), D572.1 (K), D573.1 (K), D574.1 (K), D575.1 (K), D576.1 (K)
vout_row19: D577.1 (K), D578.1 (K), D579.1 (K), D580.1 (K), D581.1 (K), D582.1 (K), D583.1 (K), D584.1 (K), D585.1 (K), D586.1 (K), D587.1 (K), D588.1 (K), D589.1 (K), D590.1 (K), D591.1 (K), D592.1 (K), D593.1 (K), D594.1 (K), D595.1 (K), D596.1 (K), D597.1 (K), D598.1 (K), D599.1 (K), D600.1 (K), D601.1 (K), D602.1 (K), D603.1 (K), D604.1 (K), D605.1 (K), D606.1 (K), D607.1 (K), D608.1 (K)
vout_row20: D609.1 (K), D610.1 (K), D611.1 (K), D612.1 (K), D613.1 (K), D614.1 (K), D615.1 (K), D616.1 (K), D617.1 (K), D618.1 (K), D619.1 (K), D620.1 (K), D621.1 (K), D622.1 (K), D623.1 (K), D624.1 (K), D625.1 (K), D626.1 (K), D627.1 (K), D628.1 (K), D629.1 (K), D630.1 (K), D631.1 (K), D632.1 (K), D633.1 (K), D634.1 (K), D635.1 (K), D636.1 (K), D637.1 (K), D638.1 (K), D639.1 (K), D640.1 (K)
vout_row21: D641.1 (K), D642.1 (K), D643.1 (K), D644.1 (K), D645.1 (K), D646.1 (K), D647.1 (K), D648.1 (K), D649.1 (K), D650.1 (K), D651.1 (K), D652.1 (K), D653.1 (K), D654.1 (K), D655.1 (K), D656.1 (K), D657.1 (K), D658.1 (K), D659.1 (K), D660.1 (K), D661.1 (K), D662.1 (K), D663.1 (K), D664.1 (K), D665.1 (K), D666.1 (K), D667.1 (K), D668.1 (K), D669.1 (K), D670.1 (K), D671.1 (K), D672.1 (K)
vout_row22: D673.1 (K), D674.1 (K), D675.1 (K), D676.1 (K), D677.1 (K), D678.1 (K), D679.1 (K), D680.1 (K), D681.1 (K), D682.1 (K), D683.1 (K), D684.1 (K), D685.1 (K), D686.1 (K), D687.1 (K), D688.1 (K), D689.1 (K), D690.1 (K), D691.1 (K), D692.1 (K), D693.1 (K), D694.1 (K), D695.1 (K), D696.1 (K), D697.1 (K), D698.1 (K), D699.1 (K), D700.1 (K), D701.1 (K), D702.1 (K), D703.1 (K), D704.1 (K)
vout_row23: D705.1 (K), D706.1 (K), D707.1 (K), D708.1 (K), D709.1 (K), D710.1 (K), D711.1 (K), D712.1 (K), D713.1 (K), D714.1 (K), D715.1 (K), D716.1 (K), D717.1 (K), D718.1 (K), D719.1 (K), D720.1 (K), D721.1 (K), D722.1 (K), D723.1 (K), D724.1 (K), D725.1 (K), D726.1 (K), D727.1 (K), D728.1 (K), D729.1 (K), D730.1 (K), D731.1 (K), D732.1 (K), D733.1 (K), D734.1 (K), D735.1 (K), D736.1 (K)
vout_row24: D737.1 (K), D738.1 (K), D739.1 (K), D740.1 (K), D741.1 (K), D742.1 (K), D743.1 (K), D744.1 (K), D745.1 (K), D746.1 (K), D747.1 (K), D748.1 (K), D749.1 (K), D750.1 (K), D751.1 (K), D752.1 (K), D753.1 (K), D754.1 (K), D755.1 (K), D756.1 (K), D757.1 (K), D758.1 (K), D759.1 (K), D760.1 (K), D761.1 (K), D762.1 (K), D763.1 (K), D764.1 (K), D765.1 (K), D766.1 (K), D767.1 (K), D768.1 (K)
vout_row25: D769.1 (K), D770.1 (K), D771.1 (K), D772.1 (K), D773.1 (K), D774.1 (K), D775.1 (K), D776.1 (K), D777.1 (K), D778.1 (K), D779.1 (K), D780.1 (K), D781.1 (K), D782.1 (K), D783.1 (K), D784.1 (K), D785.1 (K), D786.1 (K), D787.1 (K), D788.1 (K), D789.1 (K), D790.1 (K), D791.1 (K), D792.1 (K), D793.1 (K), D794.1 (K), D795.1 (K), D796.1 (K), D797.1 (K), D798.1 (K), D799.1 (K), D800.1 (K)
vout_row26: D801.1 (K), D802.1 (K), D803.1 (K), D804.1 (K), D805.1 (K), D806.1 (K), D807.1 (K), D808.1 (K), D809.1 (K), D810.1 (K), D811.1 (K), D812.1 (K), D813.1 (K), D814.1 (K), D815.1 (K), D816.1 (K), D817.1 (K), D818.1 (K), D819.1 (K), D820.1 (K), D821.1 (K), D822.1 (K), D823.1 (K), D824.1 (K), D825.1 (K), D826.1 (K), D827.1 (K), D828.1 (K), D829.1 (K), D830.1 (K), D831.1 (K), D832.1 (K)
vout_row27: D833.1 (K), D834.1 (K), D835.1 (K), D836.1 (K), D837.1 (K), D838.1 (K), D839.1 (K), D840.1 (K), D841.1 (K), D842.1 (K), D843.1 (K), D844.1 (K), D845.1 (K), D846.1 (K), D847.1 (K), D848.1 (K), D849.1 (K), D850.1 (K), D851.1 (K), D852.1 (K), D853.1 (K), D854.1 (K), D855.1 (K), D856.1 (K), D857.1 (K), D858.1 (K), D859.1 (K), D860.1 (K), D861.1 (K), D862.1 (K), D863.1 (K), D864.1 (K)
vout_row28: D865.1 (K), D866.1 (K), D867.1 (K), D868.1 (K), D869.1 (K), D870.1 (K), D871.1 (K), D872.1 (K), D873.1 (K), D874.1 (K), D875.1 (K), D876.1 (K), D877.1 (K), D878.1 (K), D879.1 (K), D880.1 (K), D881.1 (K), D882.1 (K), D883.1 (K), D884.1 (K), D885.1 (K), D886.1 (K), D887.1 (K), D888.1 (K), D889.1 (K), D890.1 (K), D891.1 (K), D892.1 (K), D893.1 (K), D894.1 (K), D895.1 (K), D896.1 (K)
vout_row29: D897.1 (K), D898.1 (K), D899.1 (K), D900.1 (K), D901.1 (K), D902.1 (K), D903.1 (K), D904.1 (K), D905.1 (K), D906.1 (K), D907.1 (K), D908.1 (K), D909.1 (K), D910.1 (K), D911.1 (K), D912.1 (K), D913.1 (K), D914.1 (K), D915.1 (K), D916.1 (K), D917.1 (K), D918.1 (K), D919.1 (K), D920.1 (K), D921.1 (K), D922.1 (K), D923.1 (K), D924.1 (K), D925.1 (K), D926.1 (K), D927.1 (K), D928.1 (K)
vout_row30: D929.1 (K), D930.1 (K), D931.1 (K), D932.1 (K), D933.1 (K), D934.1 (K), D935.1 (K), D936.1 (K), D937.1 (K), D938.1 (K), D939.1 (K), D940.1 (K), D941.1 (K), D942.1 (K), D943.1 (K), D944.1 (K), D945.1 (K), D946.1 (K), D947.1 (K), D948.1 (K), D949.1 (K), D950.1 (K), D951.1 (K), D952.1 (K), D953.1 (K), D954.1 (K), D955.1 (K), D956.1 (K), D957.1 (K), D958.1 (K), D959.1 (K), D960.1 (K)
vout_row31: D961.1 (K), D962.1 (K), D963.1 (K), D964.1 (K), D965.1 (K), D966.1 (K), D967.1 (K), D968.1 (K), D969.1 (K), D970.1 (K), D971.1 (K), D972.1 (K), D973.1 (K), D974.1 (K), D975.1 (K), D976.1 (K), D977.1 (K), D978.1 (K), D979.1 (K), D980.1 (K), D981.1 (K), D982.1 (K), D983.1 (K), D984.1 (K), D985.1 (K), D986.1 (K), D987.1 (K), D988.1 (K), D989.1 (K), D990.1 (K), D991.1 (K), D992.1 (K)
vout_row32: D993.1 (K), D994.1 (K), D995.1 (K), D996.1 (K), D997.1 (K), D998.1 (K), D999.1 (K), D1000.1 (K), D1001.1 (K), D1002.1 (K), D1003.1 (K), D1004.1 (K), D1005.1 (K), D1006.1 (K), D1007.1 (K), D1008.1 (K), D1009.1 (K), D1010.1 (K), D1011.1 (K), D1012.1 (K), D1013.1 (K), D1014.1 (K), D1015.1 (K), D1016.1 (K), D1017.1 (K), D1018.1 (K), D1019.1 (K), D1020.1 (K), D1021.1 (K), D1022.1 (K), D1023.1 (K), D1024.1 (K)

Notes on the sheet:
NOTE: 1kΩ current limiting resistors exist for only 1 column each. This works because of the way the the LED matrix is multiplexed: for every 'frame', only one row is lit at a time. So to create one image, each row is pulled to ground in quick succesion. For every row pulled to ground, paths to 3.3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
