mihirsavadi/fancyGradHat/pcb_resources/fancyGradCap_rev2/fancyGradCap_rev2_Peripherals.kicad_sch

## KiCad design pcb_resources/fancyGradCap_rev2/fancyGradCap_rev2_Peripherals.kicad_sch (2022-02-05)

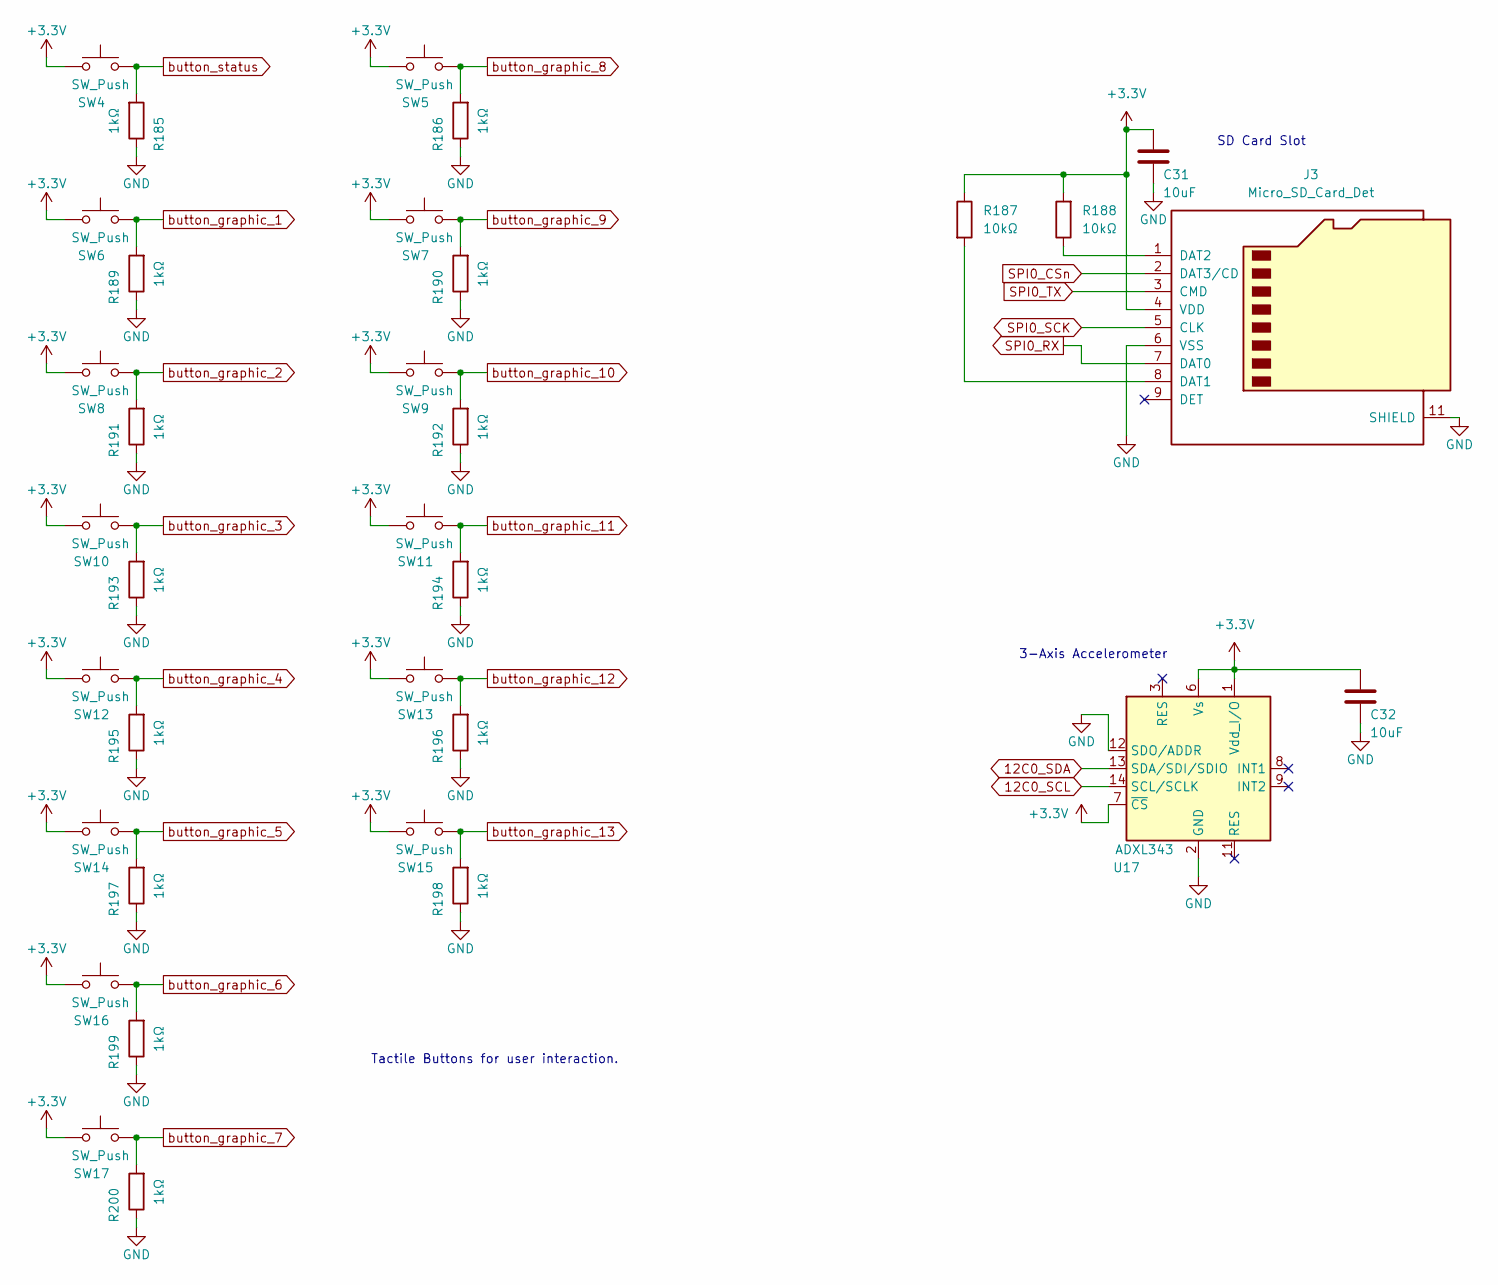
[picture p19: schematic fancyGradCap_rev2_Peripherals.kicad_sch]

Parts:
C31, C32: 10uF; C_0603_1608Metric_Pad1.08x0.95mm_HandSolder
J3: Micro_SD_Card_Det; microSDCardConnector_TF01A
R185, R186, R189, R190, R191, R192, R193, R194, R195, R196, R197, R198, R199, R200: 1kΩ; R_0603_1608Metric_Pad0.98x0.95mm_HandSolder
R187, R188: 10kΩ; R_0603_1608Metric_Pad0.98x0.95mm_HandSolder
SW4, SW5, SW6, SW7, SW8, SW9, SW10, SW11, SW12, SW13, SW14, SW15, SW16, SW17: SW_Push; SW_PUSH_1P1T_NO_6x6mm_H5mm
U17: ADXL343; ADXL343_Accelerometer

Connections:
12C0_SCL: U17.14 (SCL/SCLK)
12C0_SDA: U17.13 (SDA/SDI/SDIO)
+3.3V: C31.1, C32.1, J3.4 (VDD), R187.1, R188.2, SW4.1, SW5.1, SW6.1, SW7.1, SW8.1, SW9.1, SW10.1, SW11.1, SW12.1, SW13.1, SW14.1, SW15.1, SW16.1, SW17.1, U17.1 (Vdd_I/O), U17.6 (Vs), U17.7 (~CS)
GND: C31.2, C32.2, J3.6 (VSS), J3.11 (SHIELD), R185.1, R186.1, R189.1, R190.1, R191.1, R192.1, R193.1, R194.1, R195.1, R196.1, R197.1, R198.1, R199.1, R200.1, U17.2 (GND), U17.4 (GND), U17.5 (GND), U17.12 (SDO/ADDR)
unnamed: J3.1 (DAT2), R188.1
unnamed: J3.8 (DAT1), R187.2
SPI0_CSn: J3.2 (DAT3/CD)
SPI0_RX: J3.7 (DAT0)
SPI0_SCK: J3.5 (CLK)
SPI0_TX: J3.3 (CMD)
button_graphic_1: R189.2, SW6.2
button_graphic_2: R191.2, SW8.2
button_graphic_3: R193.2, SW10.2
button_graphic_4: R195.2, SW12.2
button_graphic_5: R197.2, SW14.2
button_graphic_6: R199.2, SW16.2
button_graphic_7: R200.2, SW17.2
button_graphic_8: R186.2, SW5.2
button_graphic_9: R190.2, SW7.2
button_graphic_10: R192.2, SW9.2
button_graphic_11: R194.2, SW11.2
button_graphic_12: R196.2, SW13.2
button_graphic_13: R198.2, SW15.2
button_status: R185.2, SW4.2

Notes on the sheet:
3-Axis Accelerometer
SD Card Slot
Tactile Buttons for user interaction.
